imyownyear/Z-Butt/community_tools/4 Sprue Stem Cavity Reservoir Part/IMG_20200822_174101 - deagcaps.jpg

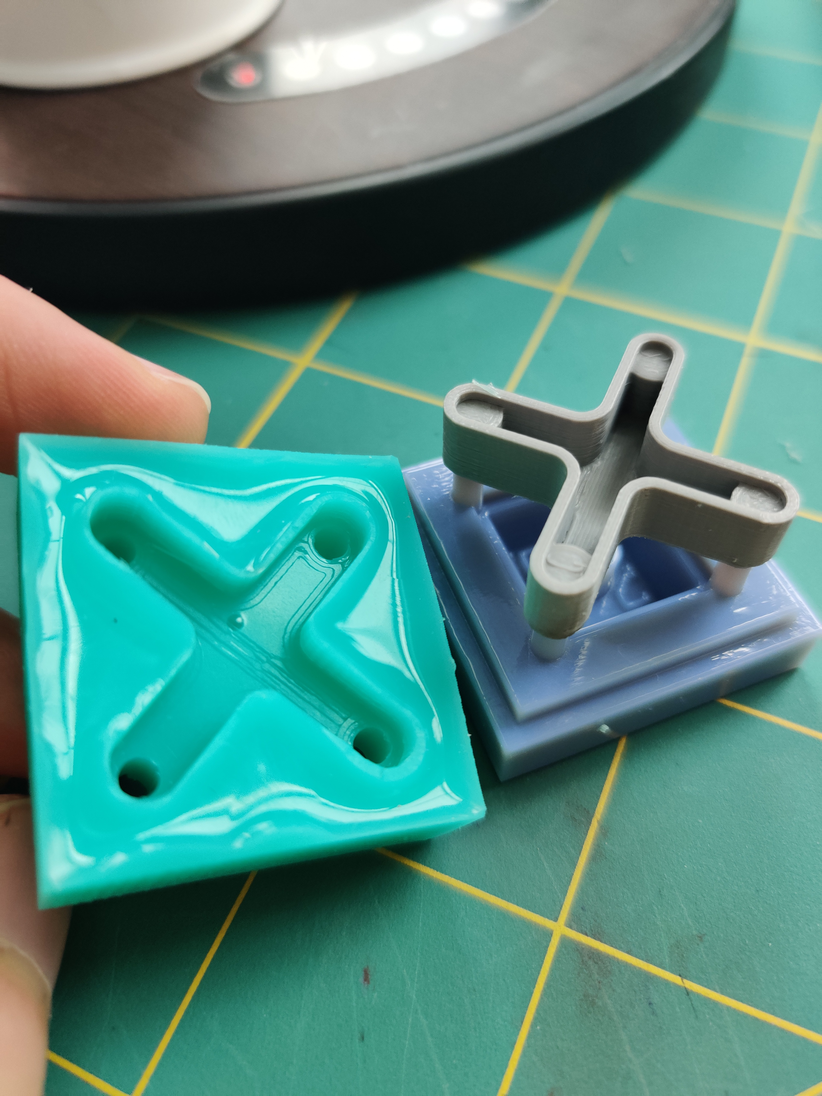
community_tools/4 Sprue Stem Cavity Reservoir Part/IMG_20200822_174101 - deagcaps.jpg
