imyownyear/Z-Butt/community_tools/6.25 Clone extender kit/20200730_202353 - Robert Maynard.jpg

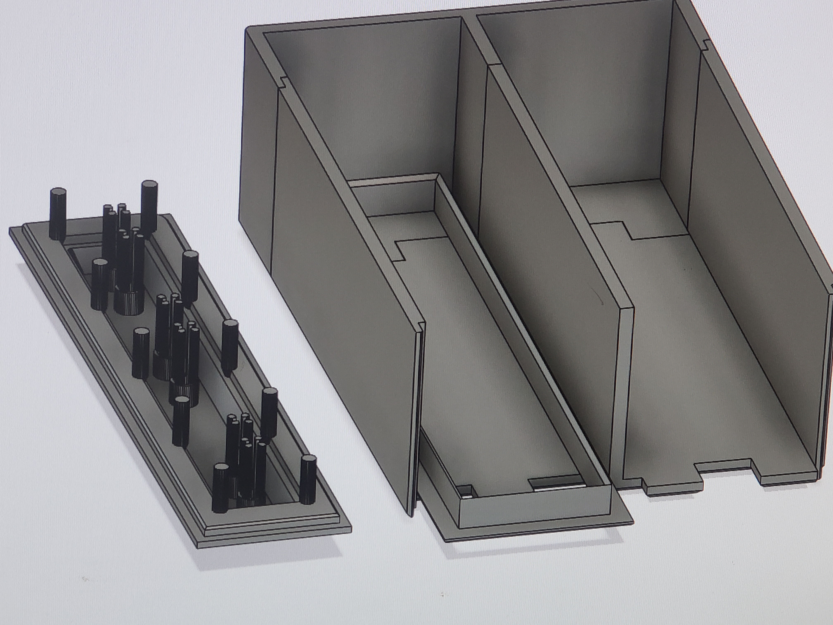
community_tools/6.25 Clone extender kit/20200730_202353 - Robert Maynard.jpg
