imyownyear/Z-Butt/MX/10-00u/ZButt-MasterBase-10u.stl

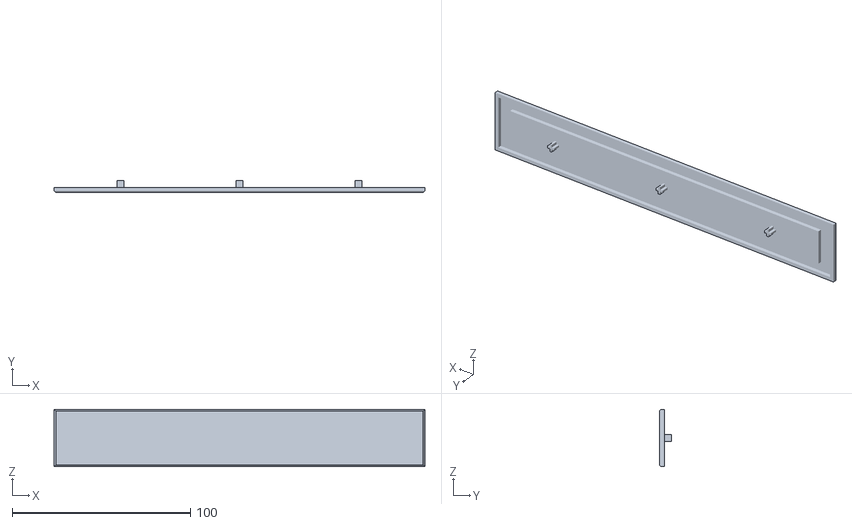
[picture p25: CAD file, 2021-09-04]
MX/10-00u/ZButt-MasterBase-10u.stl
208.0 x 7.00 x 32.0
