imyownyear/Z-Butt/MX/2-00u/V2/Reservoir.stl

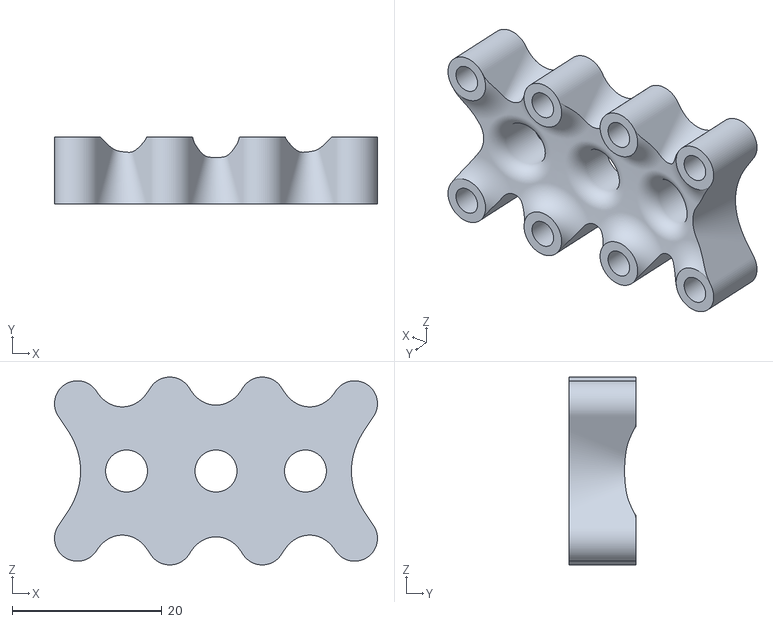
[picture p26: CAD file, 2023-01-14]
MX/2-00u/V2/Reservoir.stl
43.1 x 9.00 x 25.1
