imyownyear/Z-Butt/MX/2-25u/V2/Reservoir.stl

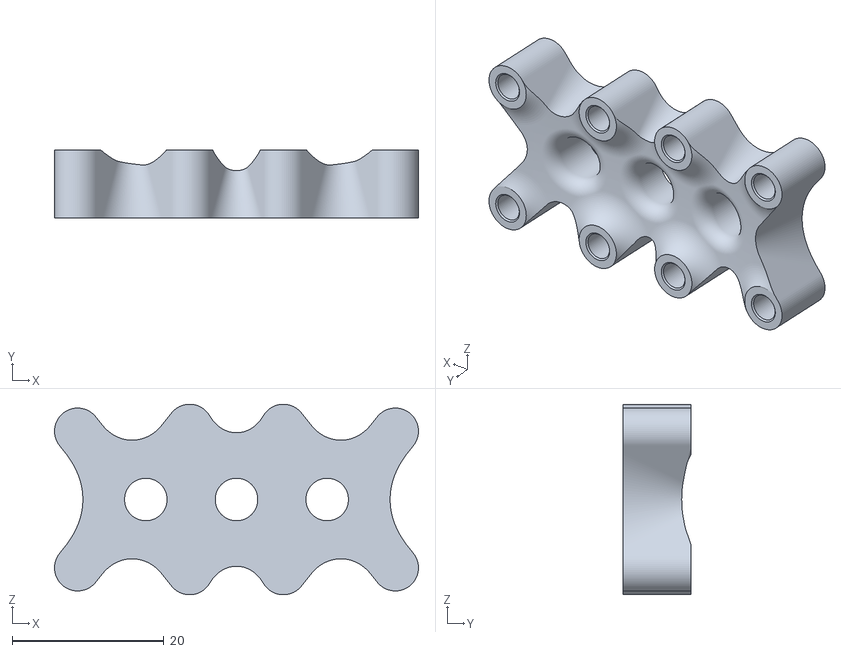
[picture p27: CAD file, 2023-01-14]
MX/2-25u/V2/Reservoir.stl
48.0 x 9.00 x 25.1
