imyownyear/Z-Butt/MX/2-50u/ZButt_2-5U_StemCavity.stl

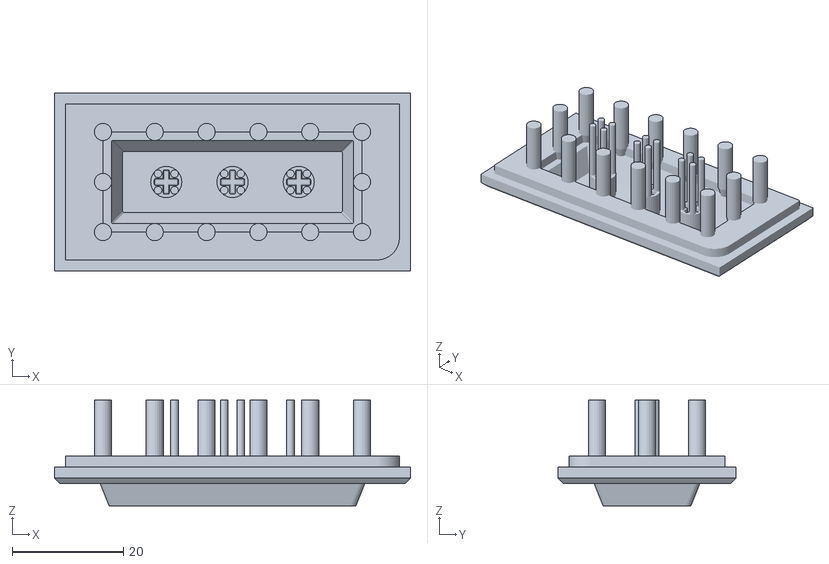
[picture p28: CAD file, 2019-06-22]
MX/2-50u/ZButt_2-5U_StemCavity.stl
64.0 x 32.0 x 19.0
