imyownyear/Z-Butt/MX/2-75u/V2/MasterBase.stl

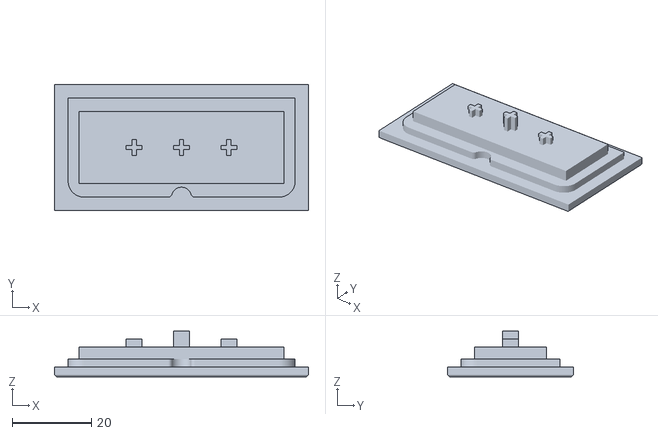
[picture p29: CAD file, 2023-01-14]
MX/2-75u/V2/MasterBase.stl
64.0 x 31.8 x 11.5
