imyownyear/Z-Butt/MX/3-00u/ZButt_3U_MasterBase.stl

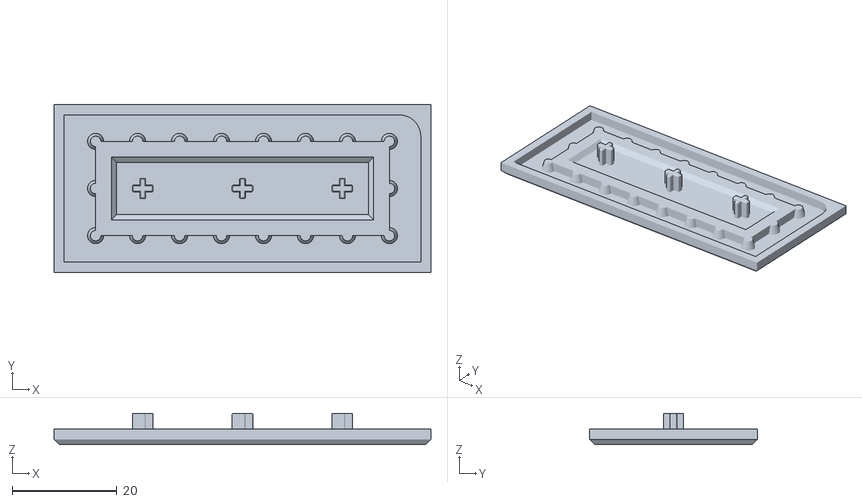
[picture p30: CAD file, 2019-06-22]
MX/3-00u/ZButt_3U_MasterBase.stl
72.0 x 32.0 x 6.00
