imyownyear/Z-Butt/MX/4-00u/ZButt_4U_StemCavity.stl

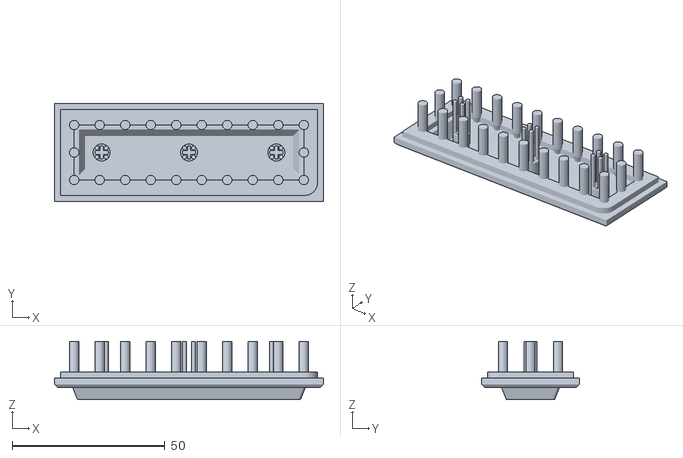
[picture p31: CAD file, 2019-06-22]
MX/4-00u/ZButt_4U_StemCavity.stl
88.0 x 32.0 x 19.0
