imyownyear/Z-Butt/MX/6-00u/ZButt_6U_StemCavity.stl

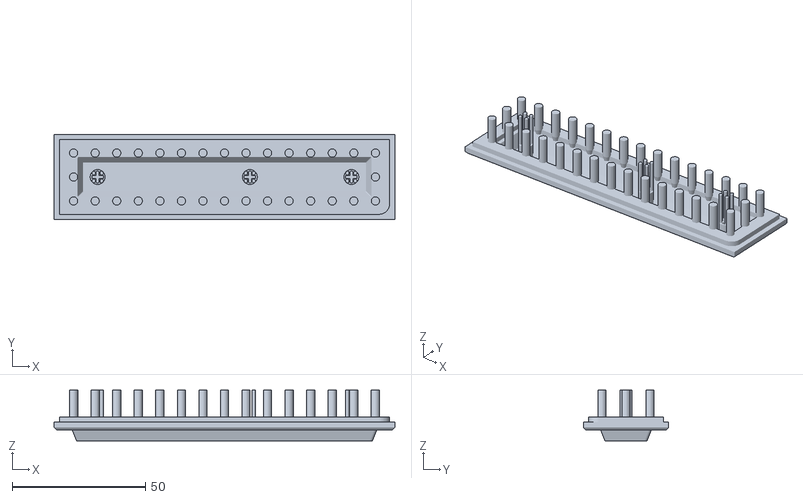
[picture p32: CAD file, 2019-06-22]
MX/6-00u/ZButt_6U_StemCavity.stl
128.0 x 32.0 x 19.0
