imyownyear/Z-Butt/MX/6-25u/V2/StemCavity.stl

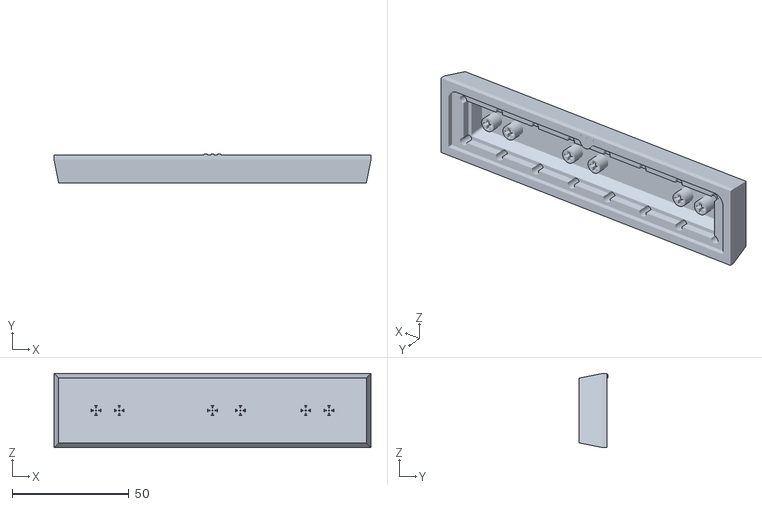
[picture p33: CAD file, 2023-01-14]
MX/6-25u/V2/StemCavity.stl
136.0 x 12.3 x 31.8
