imyownyear/Z-Butt/MX/7-00u/ZButt_7U_MasterBase.stl

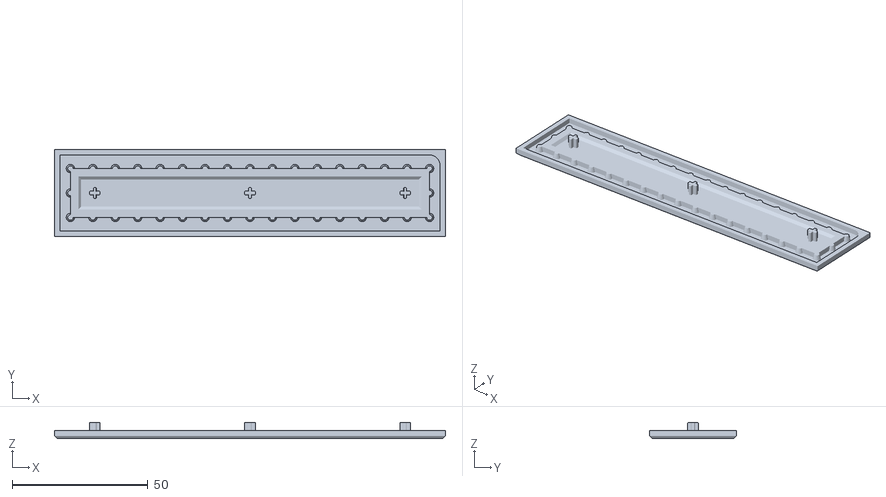
[picture p35: CAD file, 2019-06-22]
MX/7-00u/ZButt_7U_MasterBase.stl
144.0 x 32.0 x 6.00
