imyownyear/Z-Butt/MX/iso-enter/ZButt_ISO-ENTER_MasterBase-.stl

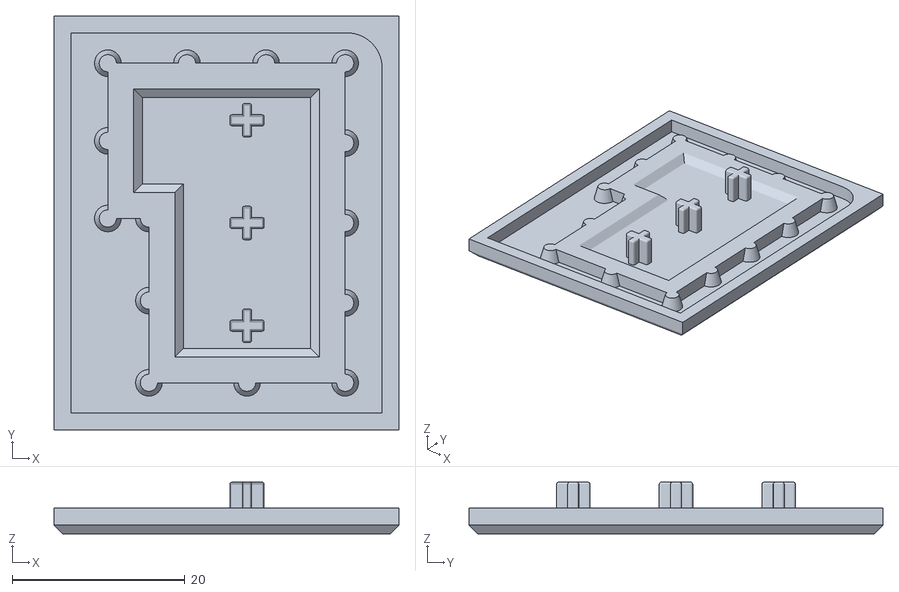
[picture p36: CAD file, 2019-07-23]
MX/iso-enter/ZButt_ISO-ENTER_MasterBase-.stl
40.0 x 48.0 x 6.00
