imyownyear/Z-Butt/NoHassleContainer/ISO-Enter-No-Hassle.stl

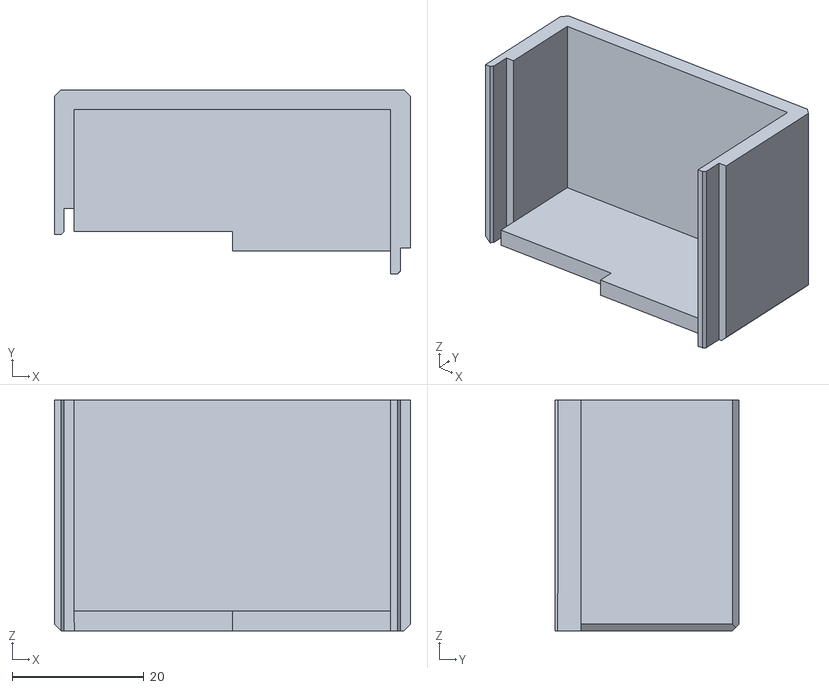
[picture p37: CAD file, 2020-08-27]
NoHassleContainer/ISO-Enter-No-Hassle.stl
54.0 x 28.0 x 35.0
