imyownyear/Z-Butt/TMX/ZButt-StemCavity.stl

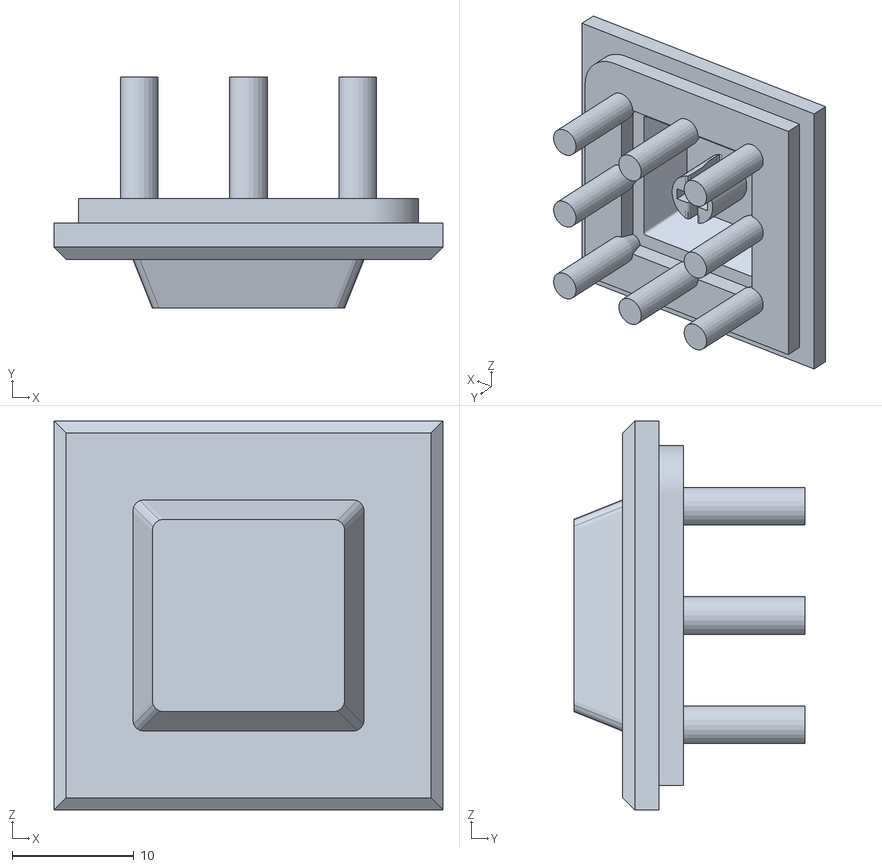
[picture p38: CAD file, 2019-08-04]
TMX/ZButt-StemCavity.stl
32.0 x 19.0 x 32.0
