imyownyear/Z-Butt/Topre/1u/v2/StemCavity.stl

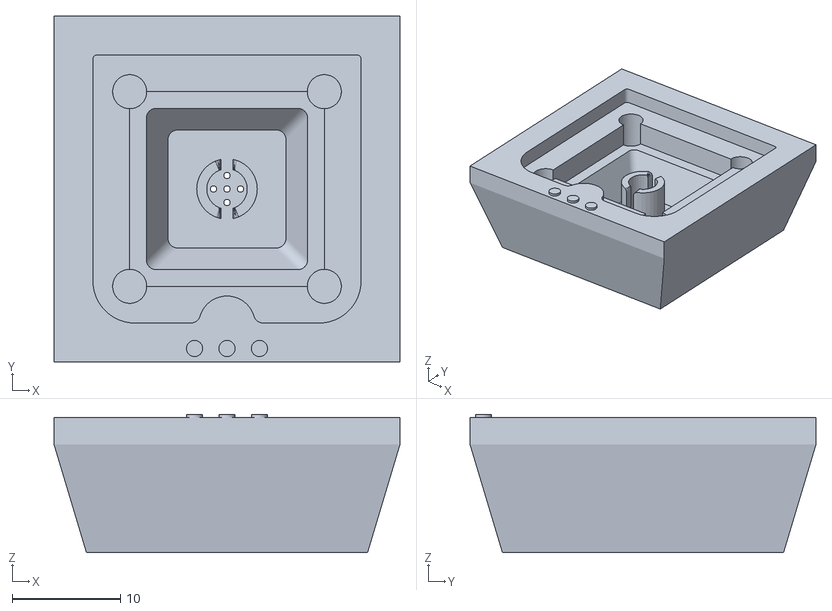
[picture p39: CAD file, 2023-01-14]
Topre/1u/v2/StemCavity.stl
32.0 x 32.0 x 12.8
