imyownyear/Z-Butt/AngleHolder/AngleHolder_4x4_A.stl

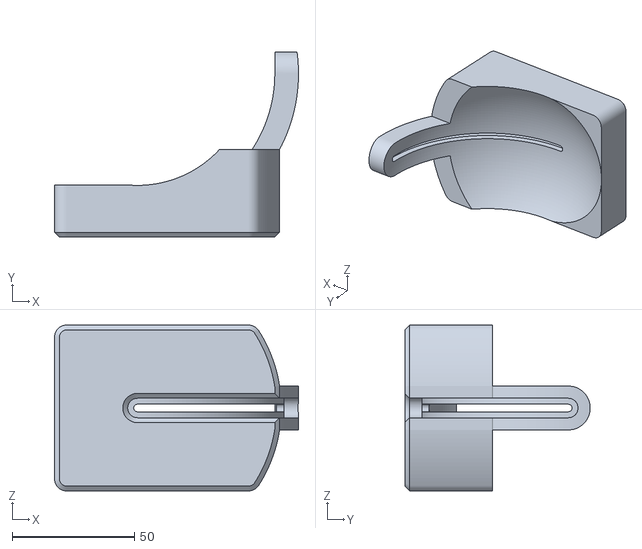
[picture p40: CAD file, 2020-08-14]
AngleHolder/AngleHolder_4x4_A.stl
100.0 x 76.0 x 68.0
