imyownyear/Z-Butt/Choc/1.5U/Choc_1.5U_SculptingBase.stl

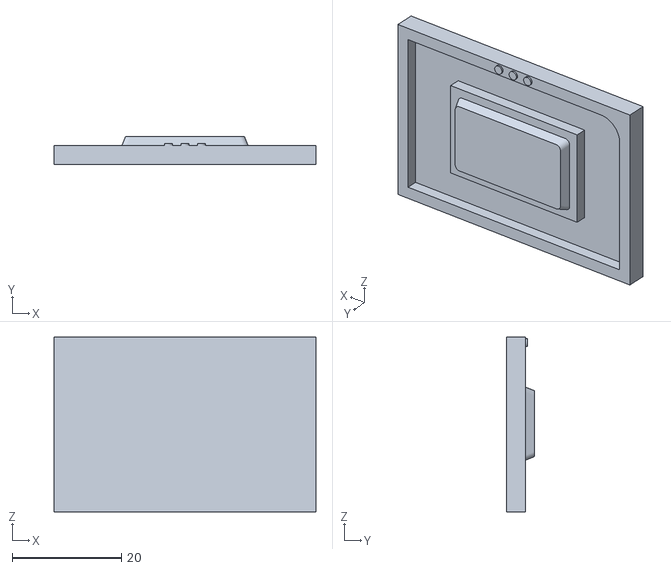
[picture p41: CAD file, 2021-09-04]
Choc/1.5U/Choc_1.5U_SculptingBase.stl
48.0 x 5.10 x 32.0
