imyownyear/Z-Butt/Choc/1U/Choc_1U_SculptingBase.stl

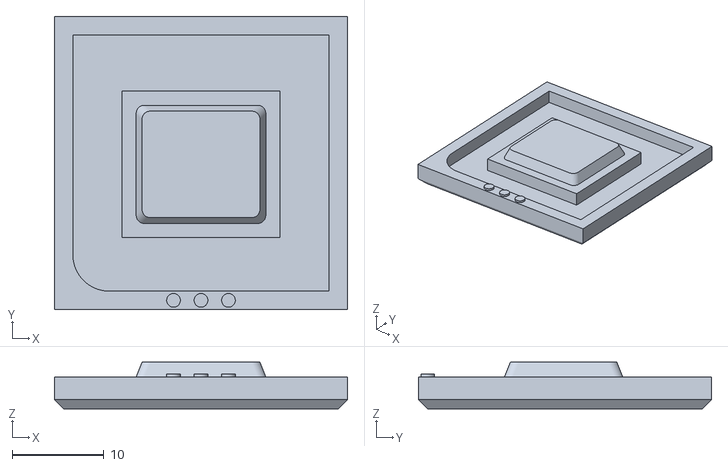
[picture p42: CAD file, 2021-09-04]
Choc/1U/Choc_1U_SculptingBase.stl
32.0 x 32.0 x 5.10
