imyownyear/Z-Butt/CloneRiser/1U/ZButt_2x2_CloneRiser_Cavity.stl

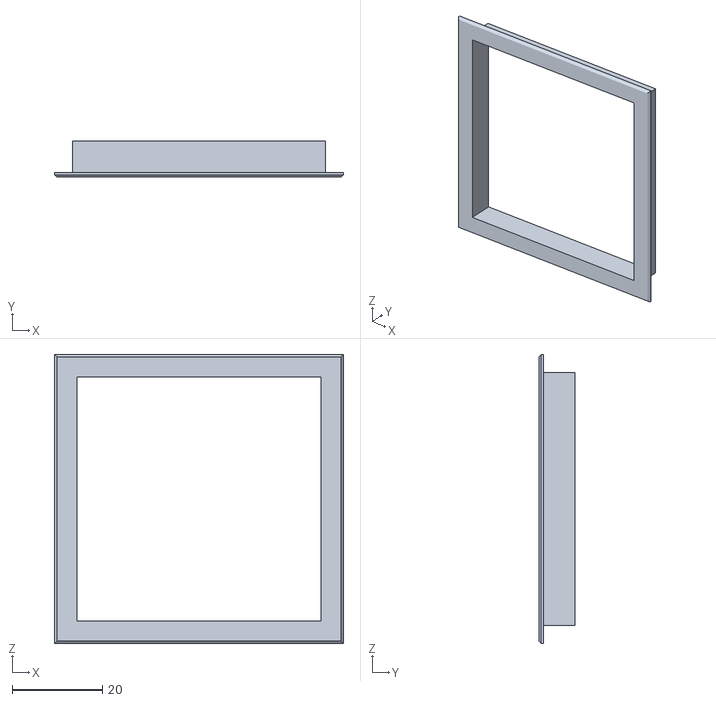
[picture p43: CAD file, 2023-01-14]
CloneRiser/1U/ZButt_2x2_CloneRiser_Cavity.stl
64.0 x 8.00 x 64.0
