imyownyear/Z-Butt/community_tools/2.75 stepped cap butt cavity and master base/Stepped Caps Stem Cavity - Robert Maynard.stl

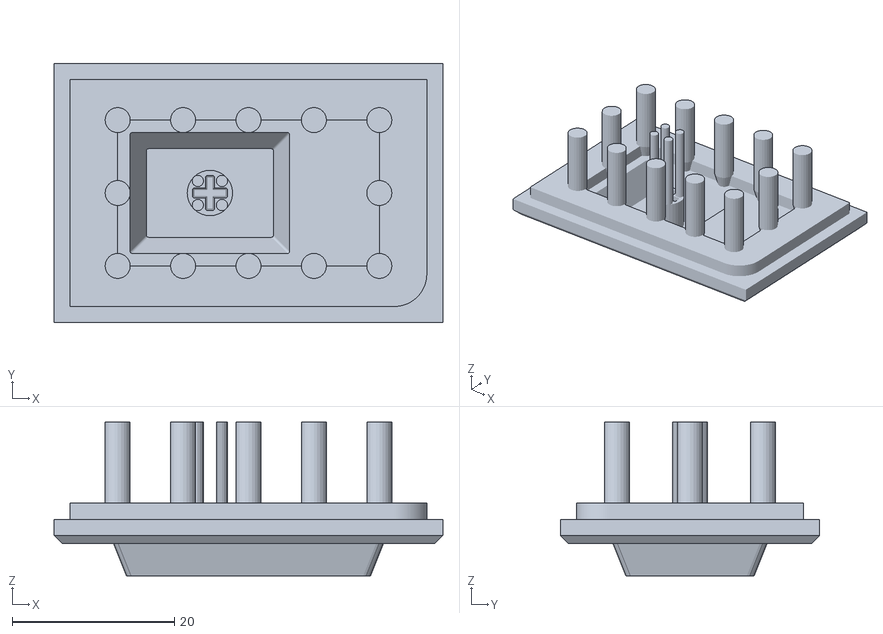
[picture p44: CAD file, 2020-09-03]
community_tools/2.75 stepped cap butt cavity and master base/Stepped Caps Stem Cavity - Robert Maynard.stl
48.0 x 32.0 x 19.0
