imyownyear/Z-Butt/community_tools/4 Sprue Stem Cavity Reservoir Part/Stem Reservoir 4 Sprue - deagcaps.STL

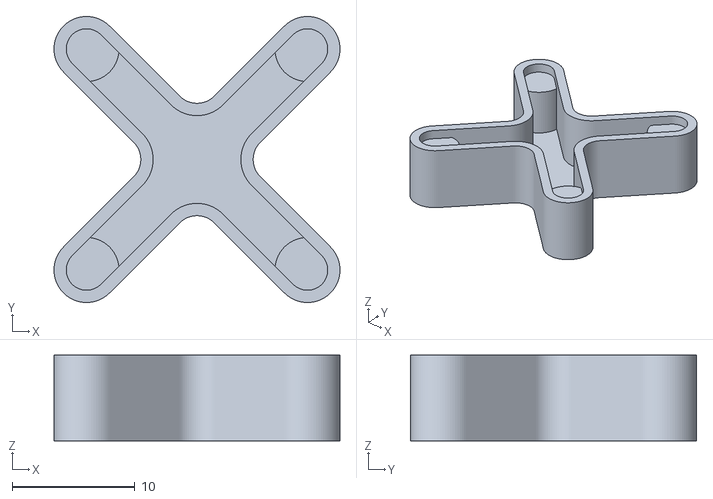
[picture p45: CAD file, 2020-09-03]
community_tools/4 Sprue Stem Cavity Reservoir Part/Stem Reservoir 4 Sprue - deagcaps.STL
23.3 x 23.3 x 7.00
