imyownyear/Z-Butt/community_tools/6.25 Clone extender kit/ZButt_6-25U_Clone_NoHassle_Extender - Robert Maynard.stl

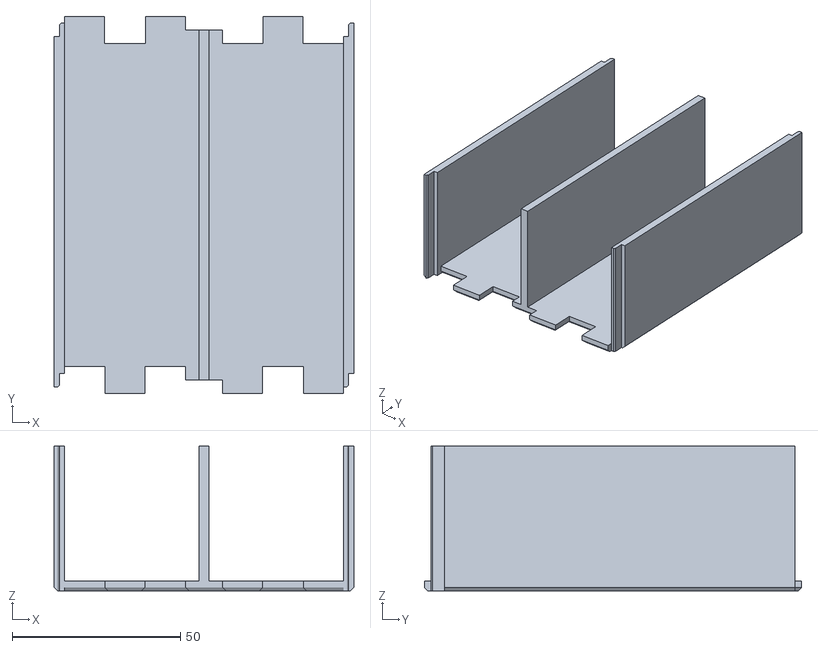
[picture p46: CAD file, 2020-09-03]
community_tools/6.25 Clone extender kit/ZButt_6-25U_Clone_NoHassle_Extender - Robert Maynard.stl
89.0 x 112.0 x 43.0
