imyownyear/Z-Butt/community_tools/Gooseneck syringe tip handle/gooseneck handle.STL

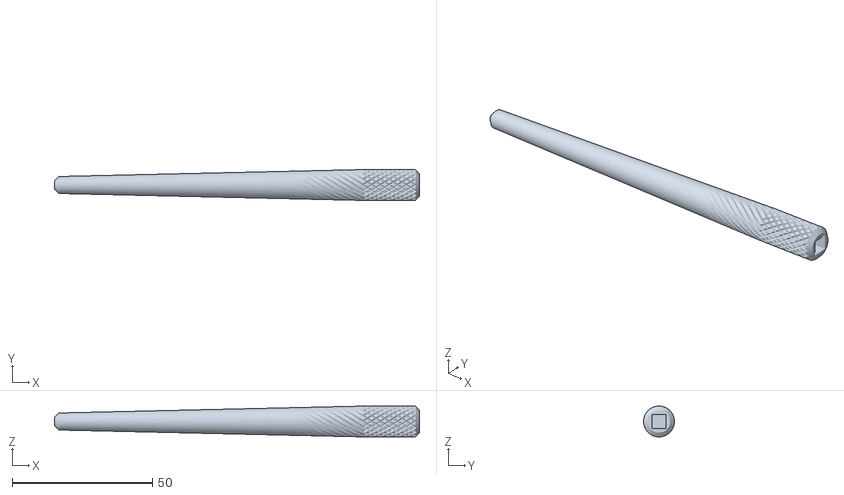
[picture p47: CAD file, 2020-09-03]
community_tools/Gooseneck syringe tip handle/gooseneck handle.STL
130.0 x 11.0 x 11.0
