imyownyear/Z-Butt/MX/1-00u/1u - Production/NoHassle2x3Extend.stl

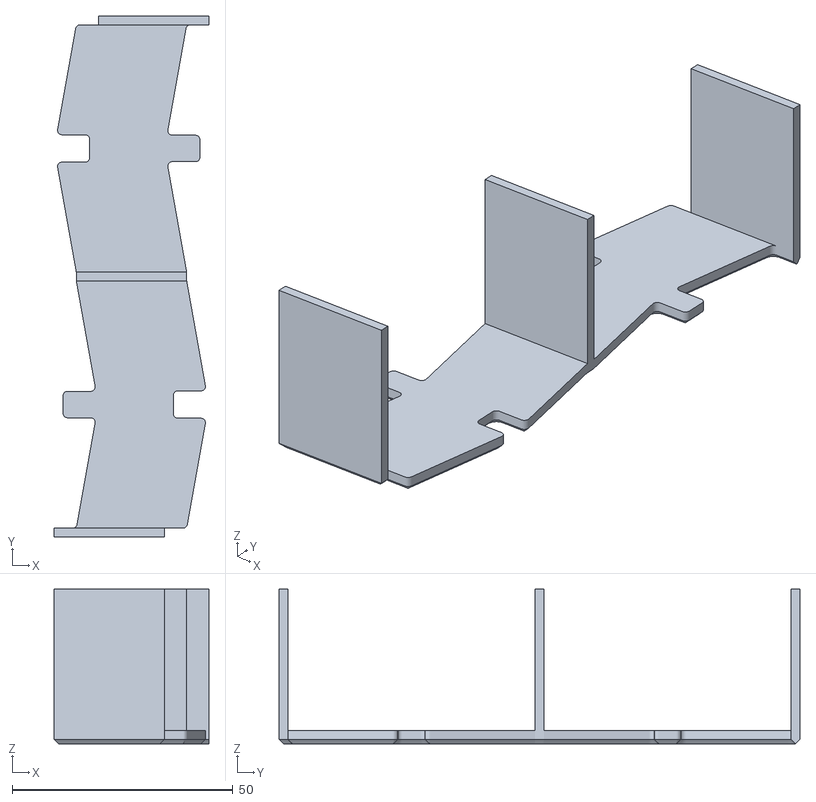
[picture p48: CAD file, 2021-12-05]
MX/1-00u/1u - Production/NoHassle2x3Extend.stl
35.0 x 118.0 x 35.0
