imyownyear/Z-Butt/MX/1-25u/V2/MasterBase.stl

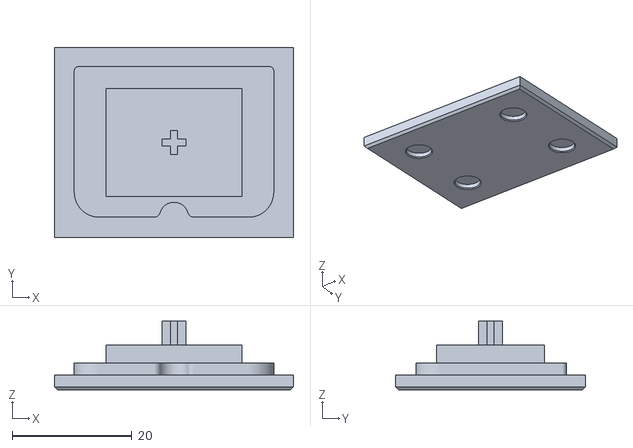
[picture p49: CAD file, 2023-01-14]
MX/1-25u/V2/MasterBase.stl
40.0 x 31.8 x 11.5
