imyownyear/Z-Butt/MX/1-50u/V2/StemCavity-Recessed.stl

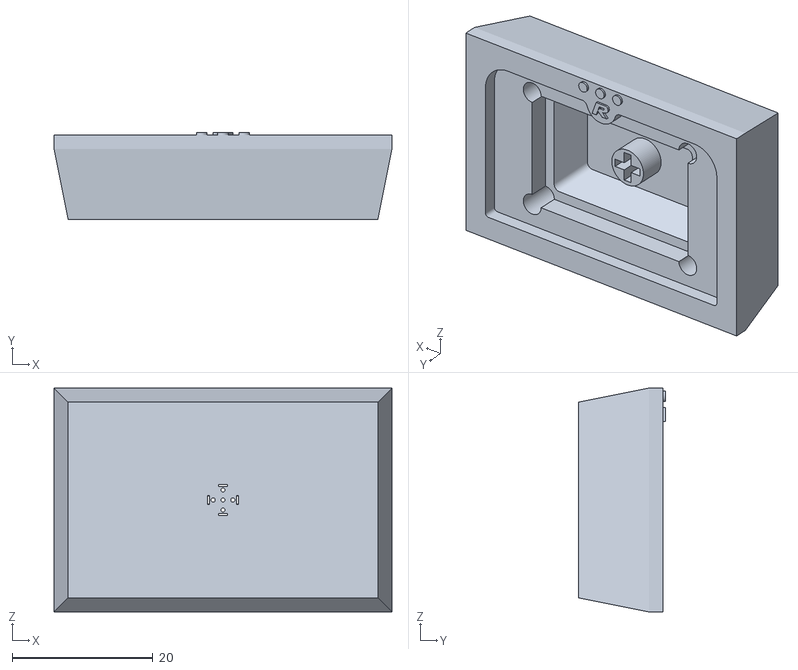
[picture p50: CAD file, 2023-01-14]
MX/1-50u/V2/StemCavity-Recessed.stl
48.0 x 12.3 x 31.8
