imyownyear/Z-Butt/MX/10-00u/ZButt-StemCavity-10u-Sprue.stl

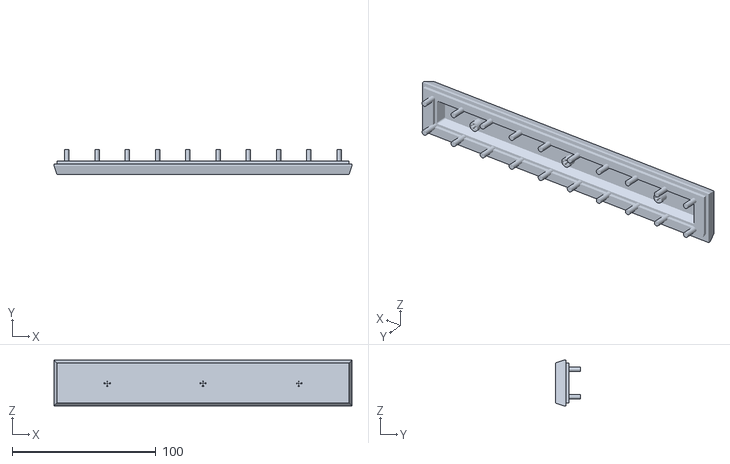
[picture p52: CAD file, 2021-09-04]
MX/10-00u/ZButt-StemCavity-10u-Sprue.stl
207.4 x 17.5 x 32.0
