imyownyear/Z-Butt/MX/2-25u/V2/StemCavity.stl

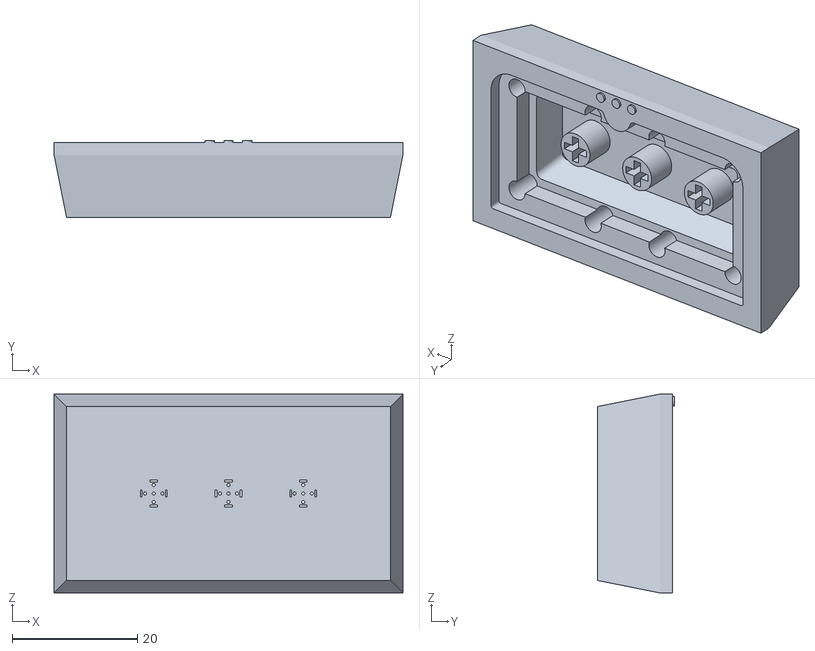
[picture p54: CAD file, 2023-01-14]
MX/2-25u/V2/StemCavity.stl
55.8 x 12.3 x 31.8
