imyownyear/Z-Butt/MX/2-75u/V2/StemCavity-Recessed.stl

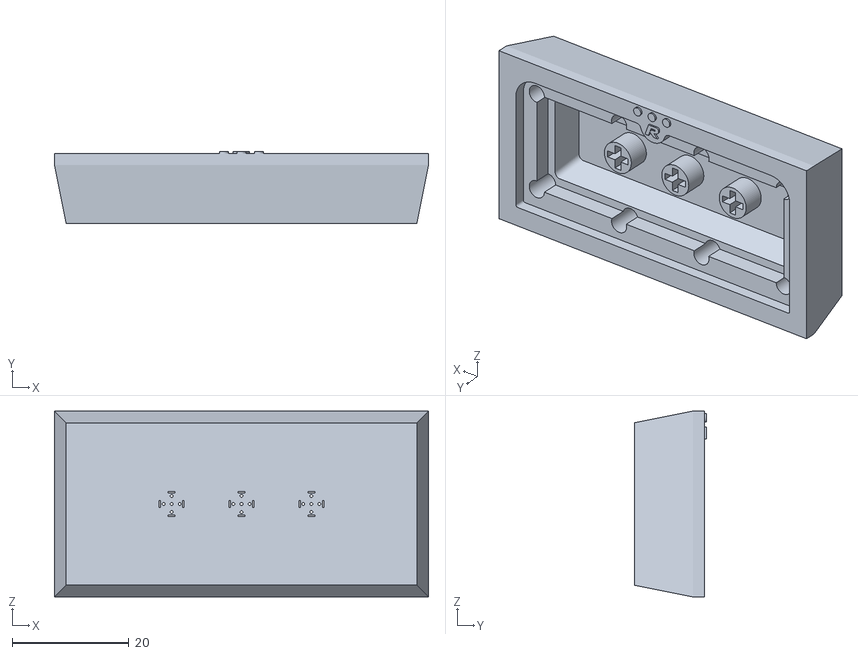
[picture p56: CAD file, 2023-01-14]
MX/2-75u/V2/StemCavity-Recessed.stl
64.0 x 12.3 x 31.8
