imyownyear/Z-Butt/MX/3-00u/ZButt_3U_StemCavity.stl

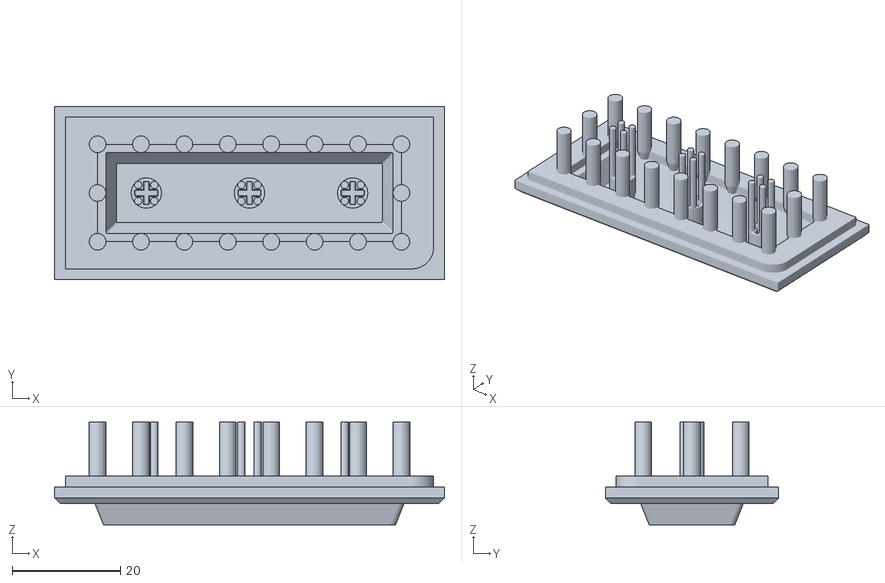
[picture p57: CAD file, 2019-06-22]
MX/3-00u/ZButt_3U_StemCavity.stl
72.0 x 32.0 x 19.0
