imyownyear/Z-Butt/MX/4-00u/ZButt_4U_SculptingBase.stl

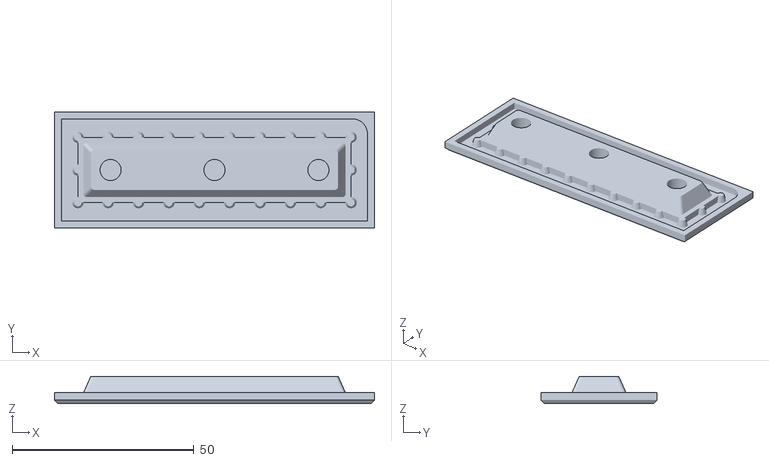
[picture p58: CAD file, 2019-06-22]
MX/4-00u/ZButt_4U_SculptingBase.stl
88.0 x 32.0 x 7.50
