imyownyear/Z-Butt/MX/6-00u/ZButt_6U_SculptingBase.stl

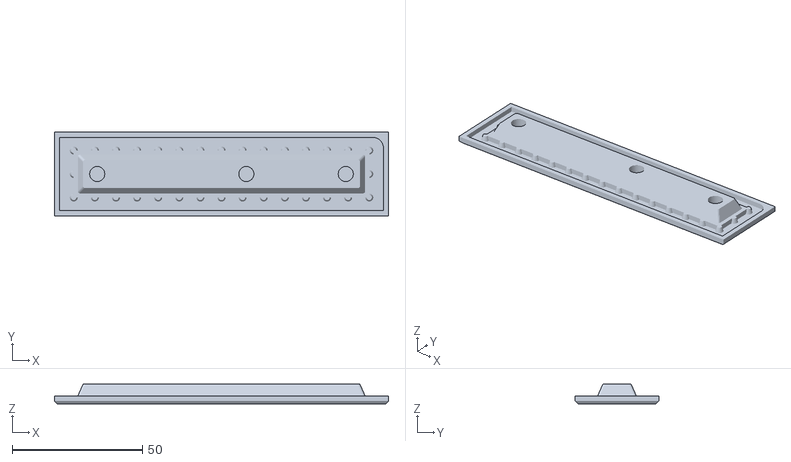
[picture p59: CAD file, 2019-06-22]
MX/6-00u/ZButt_6U_SculptingBase.stl
128.0 x 32.0 x 7.50
