imyownyear/Z-Butt/MX/6-25u/V2/MasterBase.stl

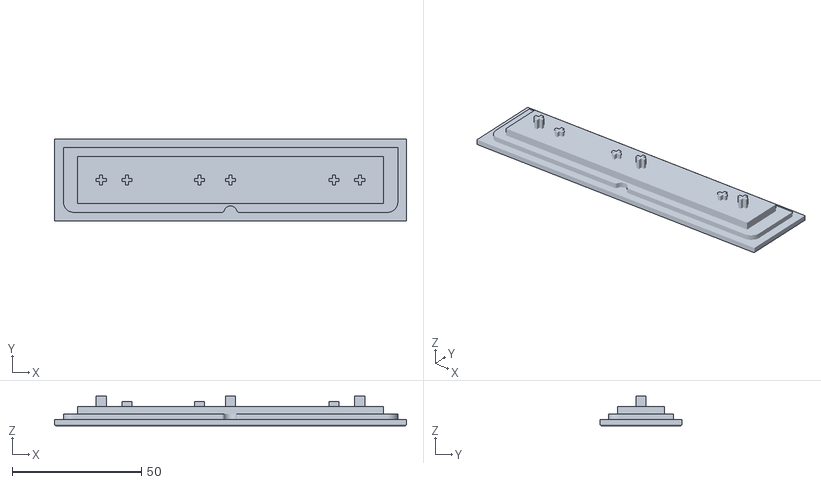
[picture p60: CAD file, 2023-01-14]
MX/6-25u/V2/MasterBase.stl
136.0 x 31.8 x 11.5
