imyownyear/Z-Butt/MX/7-00u/ZButt_7U_SculptingBase.stl

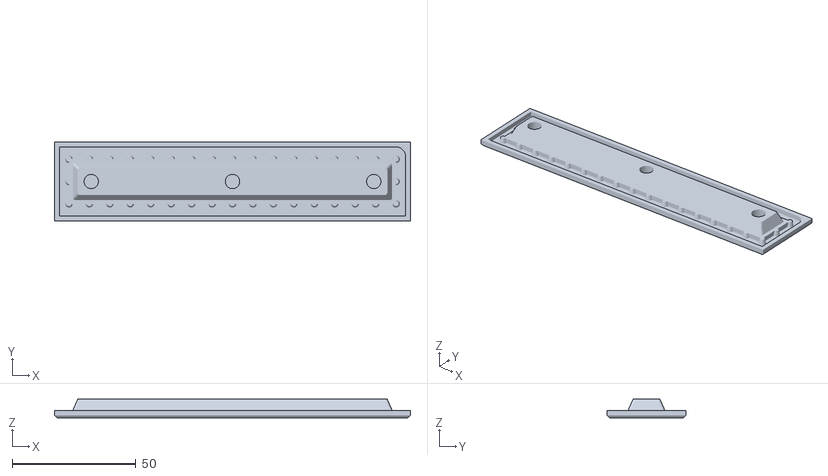
[picture p62: CAD file, 2019-06-22]
MX/7-00u/ZButt_7U_SculptingBase.stl
144.0 x 32.0 x 7.50
