imyownyear/Z-Butt/MX/iso-enter/ZButt_ISO-ENTER_SculptingBase-.stl

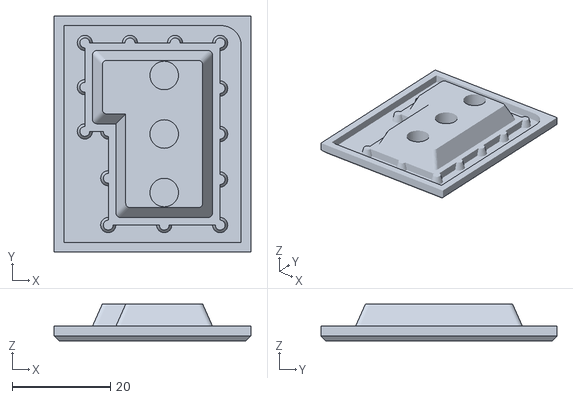
[picture p63: CAD file, 2019-07-23]
MX/iso-enter/ZButt_ISO-ENTER_SculptingBase-.stl
40.0 x 48.0 x 7.50
