imyownyear/Z-Butt/NoHassleContainer/1.25U-1.5U-No-Hassle.STL

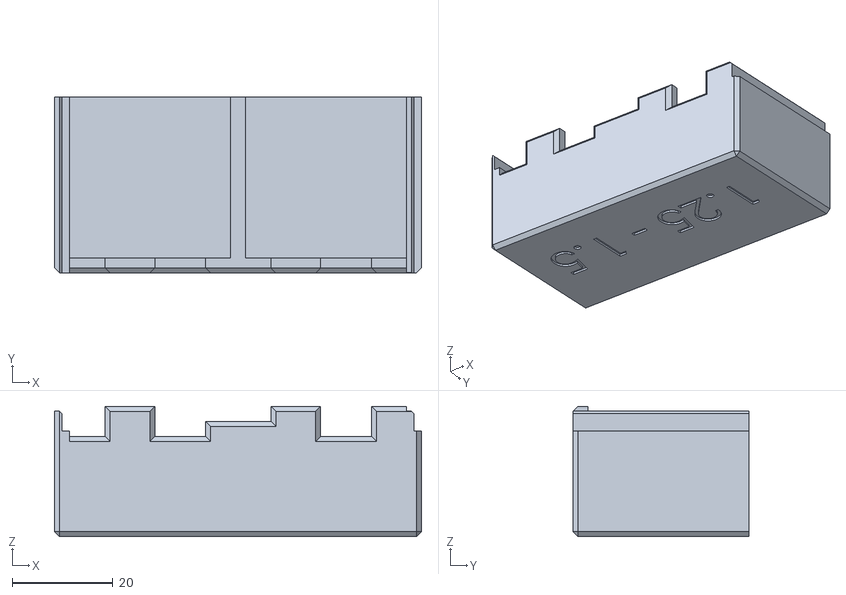
[picture p64: CAD file, 2020-07-30]
NoHassleContainer/1.25U-1.5U-No-Hassle.STL
73.0 x 35.0 x 26.0
