imyownyear/Z-Butt/AngleHolder/AngleHolder_1x1U.stl

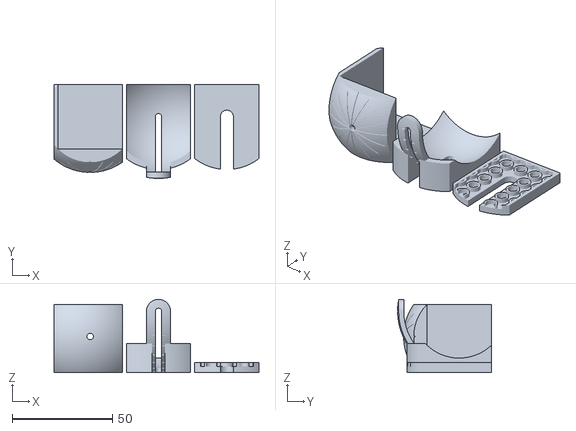
[picture p65: CAD file, 2020-08-12]
AngleHolder/AngleHolder_1x1U.stl
102.0 x 46.7 x 36.5
