imyownyear/Z-Butt/Choc/1U/Choc_1U_MasterBase.stl

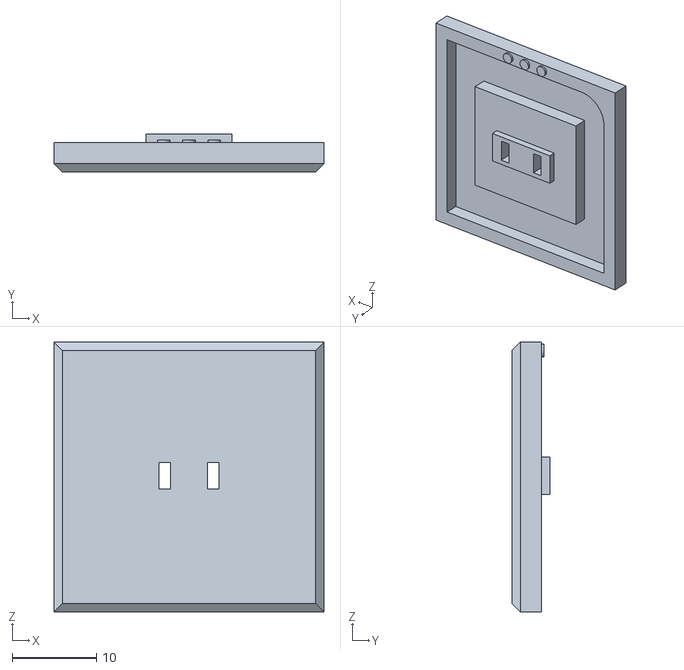
[picture p66: CAD file, 2021-09-04]
Choc/1U/Choc_1U_MasterBase.stl
32.0 x 4.50 x 32.0
