imyownyear/Z-Butt/Choc/2U/Choc_2U_StemCavity.stl

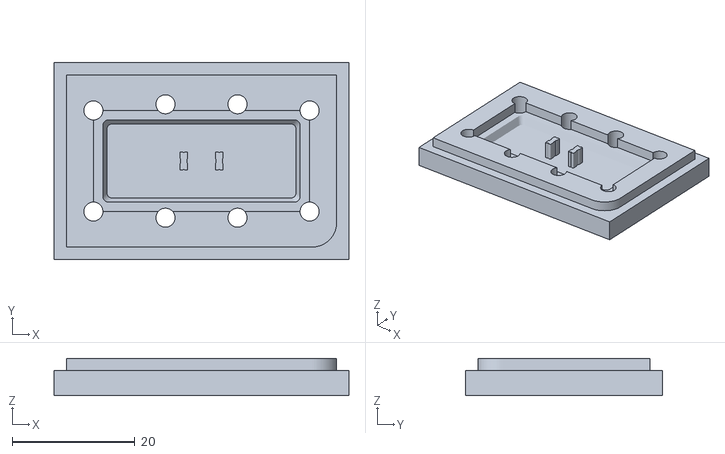
[picture p67: CAD file, 2021-09-04]
Choc/2U/Choc_2U_StemCavity.stl
48.0 x 32.0 x 6.10
