imyownyear/Z-Butt/CloneRiser/1U/ZButt_1U_Clone_NoHassle.STL

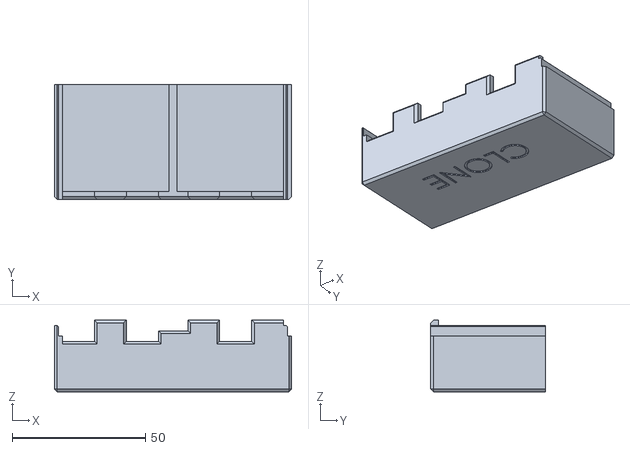
[picture p68: CAD file, 2020-02-06]
CloneRiser/1U/ZButt_1U_Clone_NoHassle.STL
89.0 x 43.0 x 27.0
