imyownyear/Z-Butt/community_tools/6.25 Clone extender kit/ZButt_6-25U_CloneRiser_Master - Robert Maynard.stl

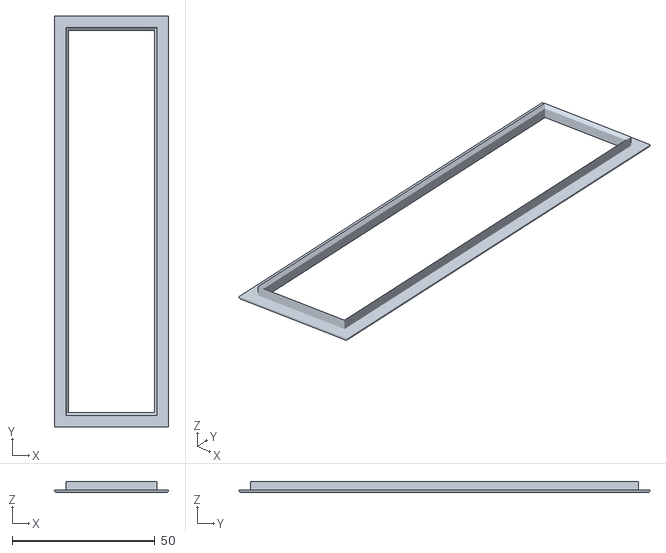
[picture p69: CAD file, 2020-09-03]
community_tools/6.25 Clone extender kit/ZButt_6-25U_CloneRiser_Master - Robert Maynard.stl
40.0 x 144.0 x 4.00
