imyownyear/Z-Butt/MX/1-00u/1u - Production/ZButt-StemCavity-2x3-Recessed.stl

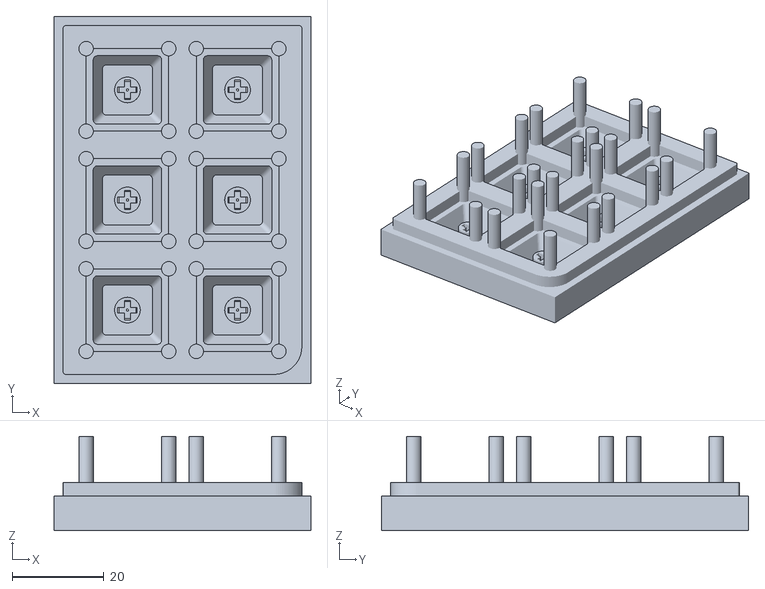
[picture p70: CAD file, 2021-11-26]
MX/1-00u/1u - Production/ZButt-StemCavity-2x3-Recessed.stl
56.0 x 80.0 x 20.5
