imyownyear/Z-Butt/MX/1-00u/1u-V2/1u-Resevoir-Topper-0.3.stl

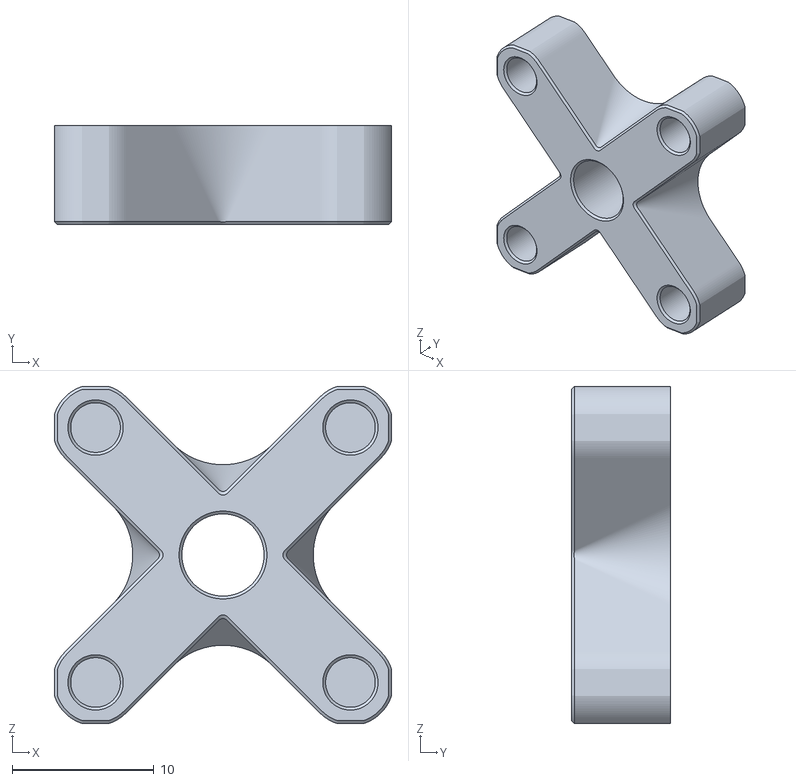
[picture p71: CAD file, 2021-03-12]
MX/1-00u/1u-V2/1u-Resevoir-Topper-0.3.stl
23.8 x 7.00 x 23.8
