imyownyear/Z-Butt/MX/1-25u/V2/Reservoir.stl

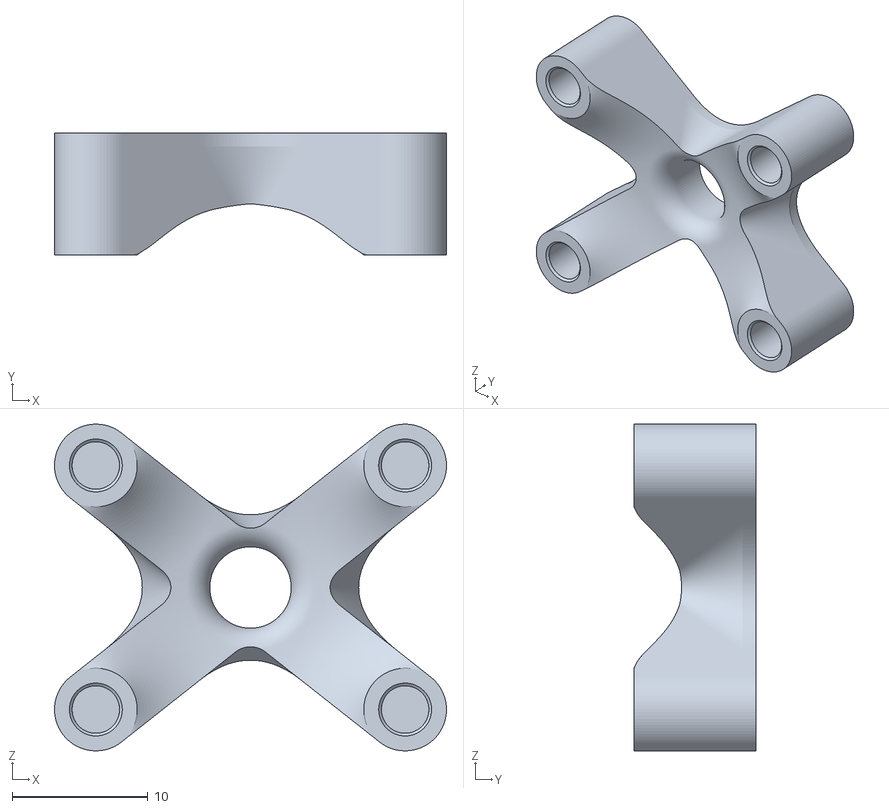
[picture p72: CAD file, 2023-01-14]
MX/1-25u/V2/Reservoir.stl
28.9 x 9.00 x 24.1
