imyownyear/Z-Butt/MX/1-50u/V2/MasterBase.stl

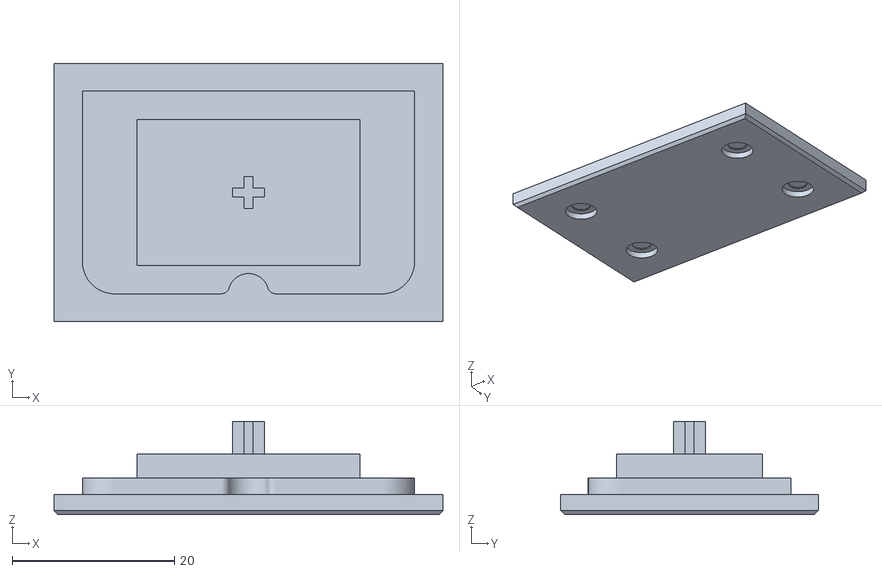
[picture p73: CAD file, 2023-01-14]
MX/1-50u/V2/MasterBase.stl
48.0 x 31.8 x 11.5
