imyownyear/Z-Butt/MX/1-75u/V2/StemCavity.stl

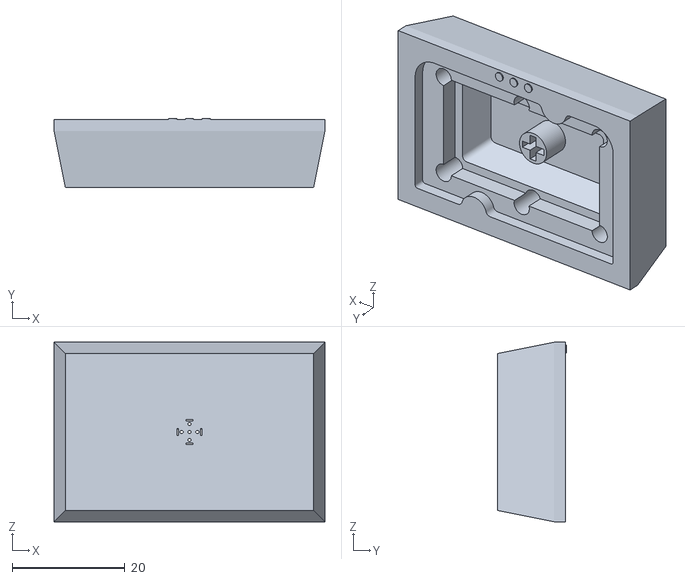
[picture p74: CAD file, 2023-01-14]
MX/1-75u/V2/StemCavity.stl
48.0 x 12.2 x 31.8
