imyownyear/Z-Butt/MX/10-00u/Zbutt-SculptingBase-10u.stl

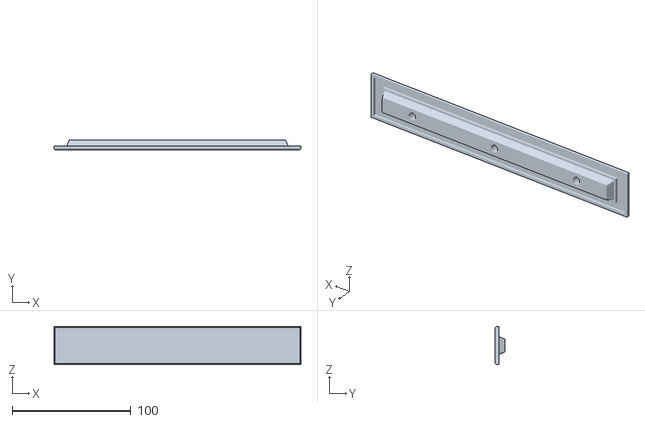
[picture p75: CAD file, 2021-09-04]
MX/10-00u/Zbutt-SculptingBase-10u.stl
208.0 x 8.00 x 32.0
