imyownyear/Z-Butt/MX/2-00u/V2/MasterBase.stl

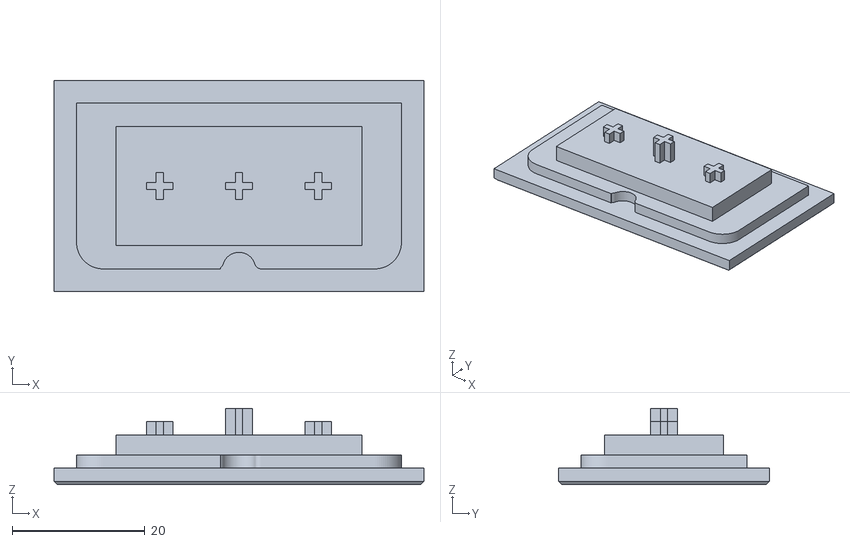
[picture p76: CAD file, 2023-01-14]
MX/2-00u/V2/MasterBase.stl
55.8 x 31.8 x 11.5
