imyownyear/Z-Butt/MX/2-50u/ZButt_2-5U_SculptingBase.stl

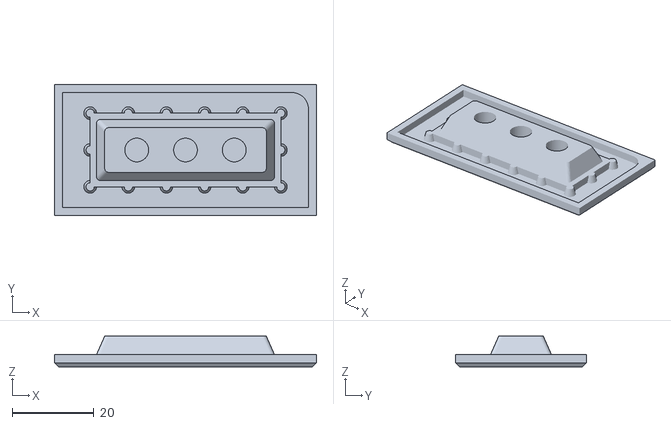
[picture p77: CAD file, 2019-06-22]
MX/2-50u/ZButt_2-5U_SculptingBase.stl
64.0 x 32.0 x 7.50
