imyownyear/Z-Butt/MX/2-75u/V2/Reservoir.stl

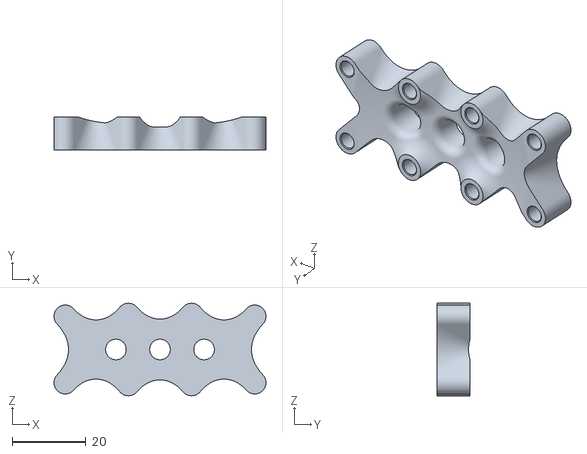
[picture p78: CAD file, 2023-01-14]
MX/2-75u/V2/Reservoir.stl
57.5 x 9.00 x 25.1
