imyownyear/Z-Butt/MX/3-00u/ZButt_3U_SculptingBase.stl

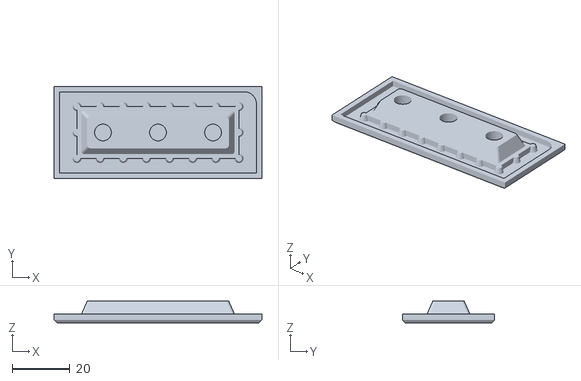
[picture p79: CAD file, 2019-06-22]
MX/3-00u/ZButt_3U_SculptingBase.stl
72.0 x 32.0 x 7.50
