imyownyear/Z-Butt/MX/4-00u/ZButt_4U_MasterBase.stl

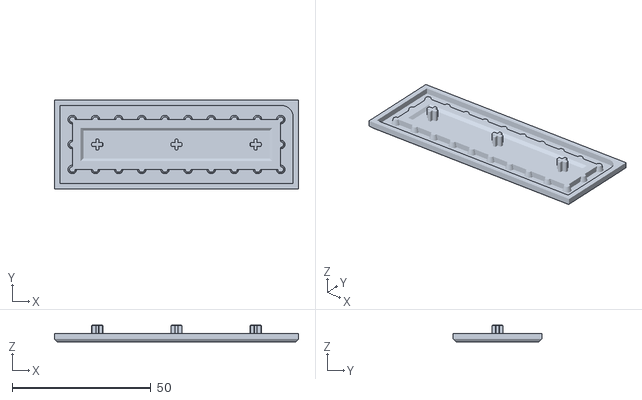
[picture p80: CAD file, 2019-06-22]
MX/4-00u/ZButt_4U_MasterBase.stl
88.0 x 32.0 x 6.00
