imyownyear/Z-Butt/MX/6-00u/ZButt_6U_MasterBase.stl

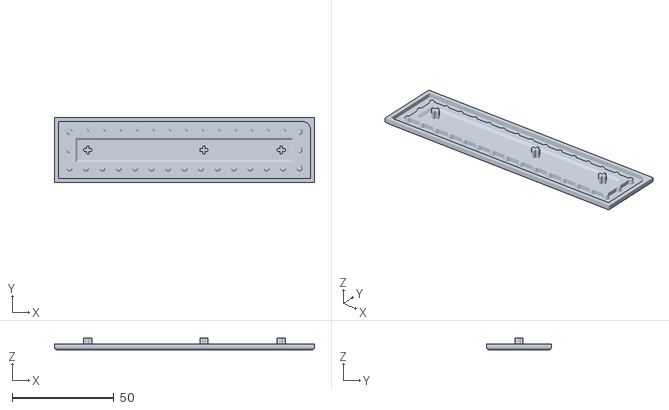
[picture p81: CAD file, 2019-06-22]
MX/6-00u/ZButt_6U_MasterBase.stl
128.0 x 32.0 x 6.00
