imyownyear/Z-Butt/MX/6-25u/V2/SculptingBase.stl

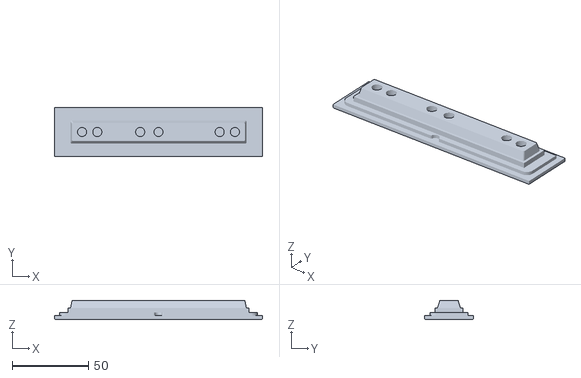
[picture p82: CAD file, 2023-01-14]
MX/6-25u/V2/SculptingBase.stl
136.0 x 31.8 x 12.5
