imyownyear/Z-Butt/MX/6-50u/SA-6.5u-OnMasterBase.stl

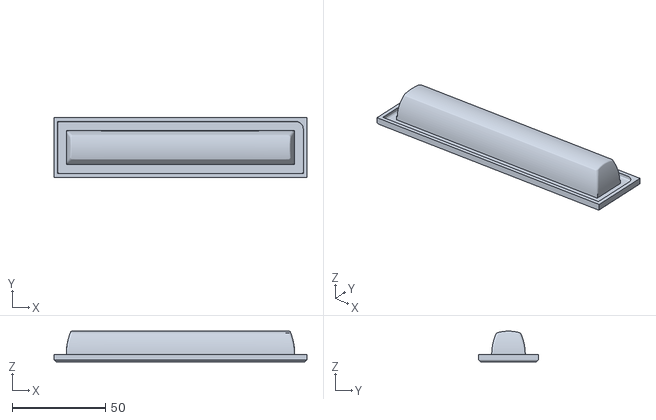
[picture p83: CAD file, 2021-09-03]
MX/6-50u/SA-6.5u-OnMasterBase.stl
136.0 x 32.0 x 16.5
