imyownyear/Z-Butt/MX/7-00u/ZButt_7U_StemCavity.stl

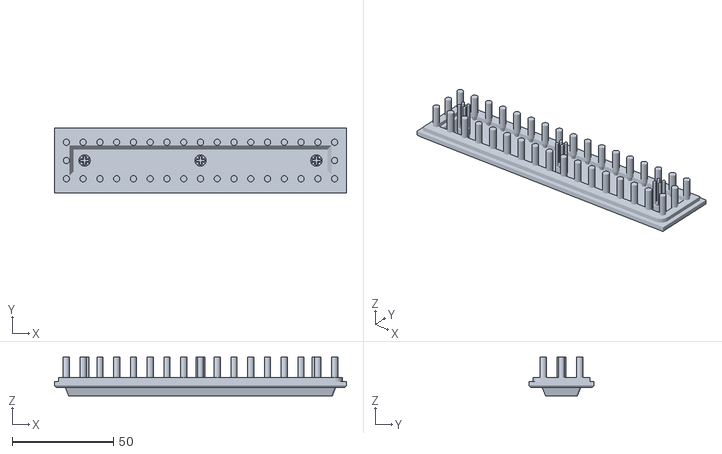
[picture p84: CAD file, 2019-06-22]
MX/7-00u/ZButt_7U_StemCavity.stl
144.0 x 32.0 x 19.0
