imyownyear/Z-Butt/MX/iso-enter/ZButt_ISO-ENTER_StemCavity-.stl

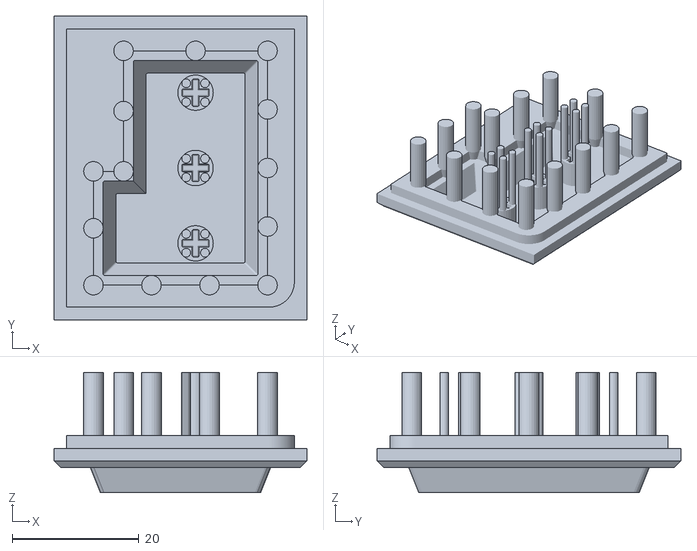
[picture p85: CAD file, 2019-07-23]
MX/iso-enter/ZButt_ISO-ENTER_StemCavity-.stl
40.0 x 48.0 x 19.0
