imyownyear/Z-Butt/NoHassleContainer/2.50U-2.75U-No-Hassle.STL

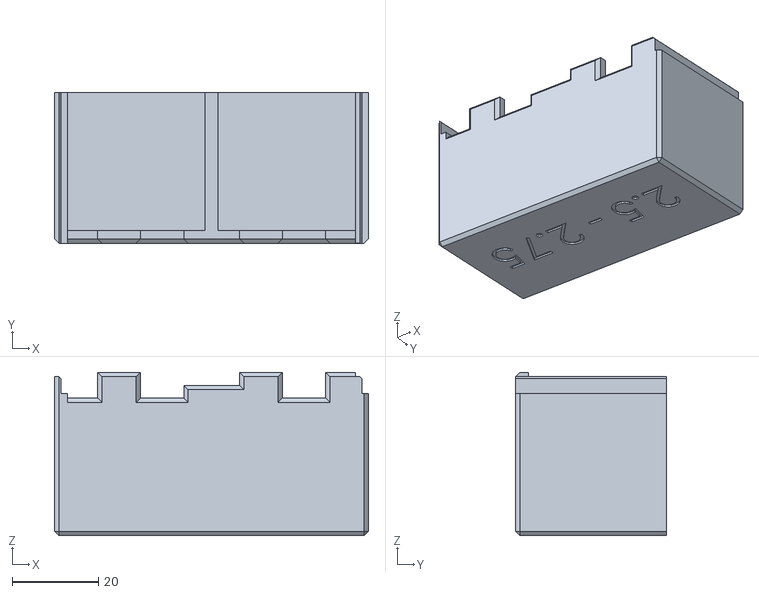
[picture p86: CAD file, 2020-07-30]
NoHassleContainer/2.50U-2.75U-No-Hassle.STL
73.0 x 35.0 x 38.0
