imyownyear/Z-Butt/CloneRiser/1U/ZButt_1U_CloneRiser_Master.stl

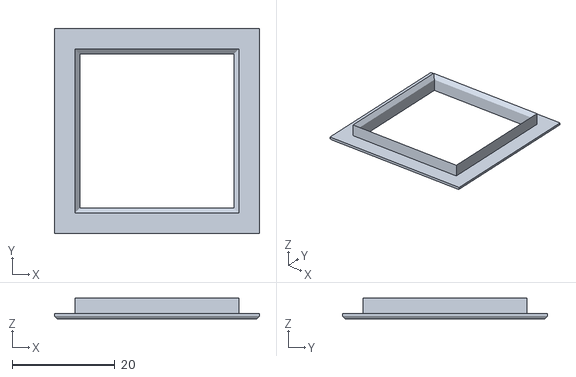
[picture p87: CAD file, 2019-08-20]
CloneRiser/1U/ZButt_1U_CloneRiser_Master.stl
40.0 x 40.0 x 4.00
