imyownyear/Z-Butt/MX/1-00u/1u - Production/ZButt-MasterBase-2x3 .stl

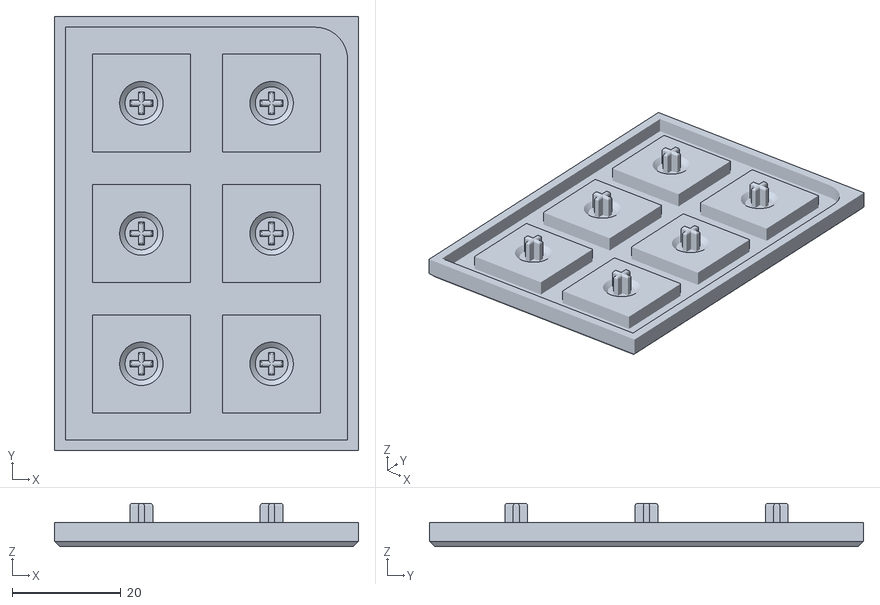
[picture p88: CAD file, 2021-11-26]
MX/1-00u/1u - Production/ZButt-MasterBase-2x3 .stl
56.0 x 80.0 x 8.00
