imyownyear/Z-Butt/MX/1-00u/1u-V2/MasterBase.stl

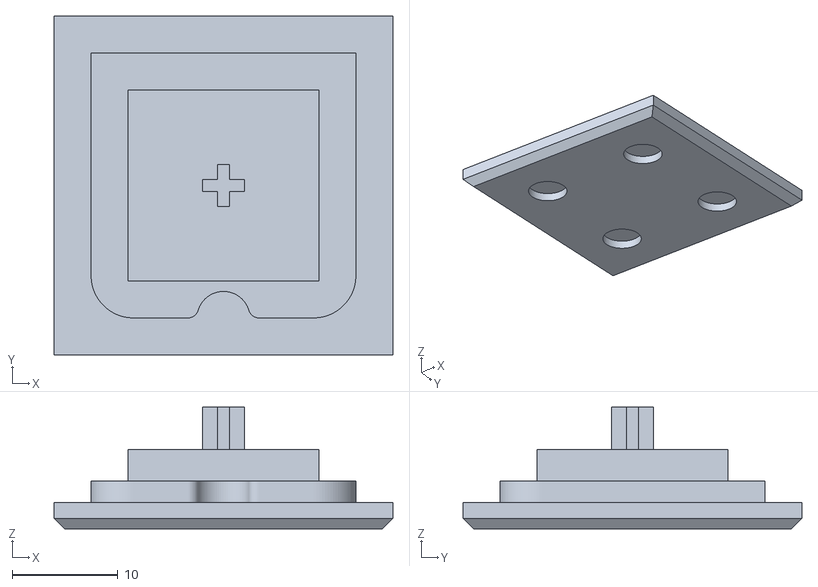
[picture p89: CAD file, 2021-03-12]
MX/1-00u/1u-V2/MasterBase.stl
32.0 x 32.0 x 11.5
