imyownyear/Z-Butt/MX/1-25u/V2/StemCavity.stl

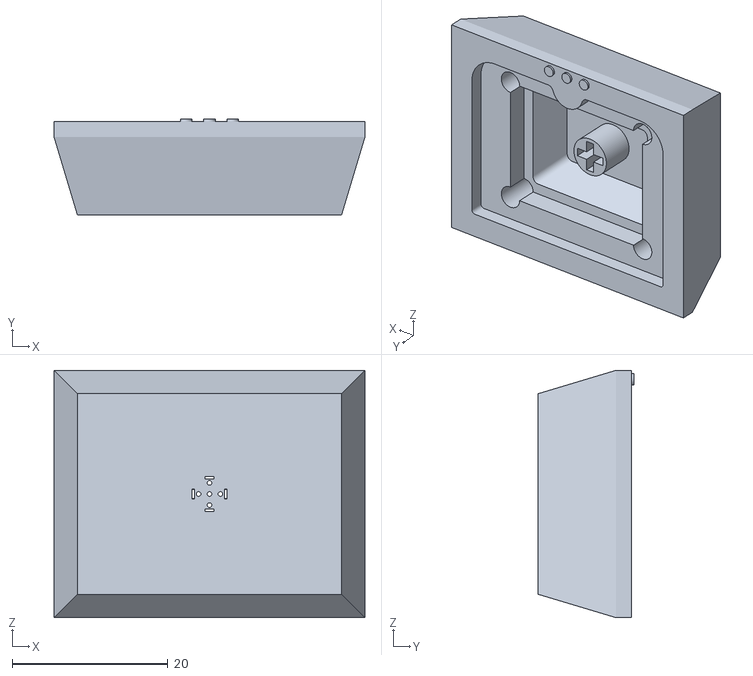
[picture p90: CAD file, 2023-01-14]
MX/1-25u/V2/StemCavity.stl
40.0 x 12.3 x 31.8
