imyownyear/Z-Butt/MX/2-00u/V2/StemCavity-Recessed.stl

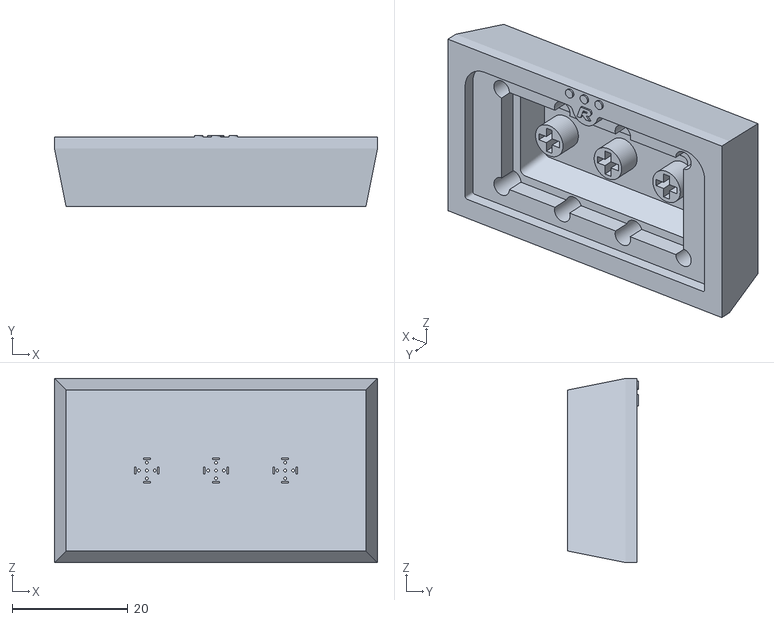
[picture p92: CAD file, 2023-01-14]
MX/2-00u/V2/StemCavity-Recessed.stl
55.8 x 12.3 x 31.8
