imyownyear/Z-Butt/MX/2-75u/V2/SculptingBase.stl

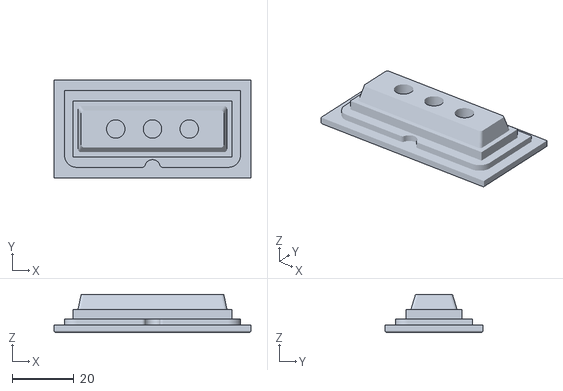
[picture p93: CAD file, 2023-01-14]
MX/2-75u/V2/SculptingBase.stl
64.0 x 31.8 x 12.5
