imyownyear/Z-Butt/MX/6-25u/V2/Reservoir.stl

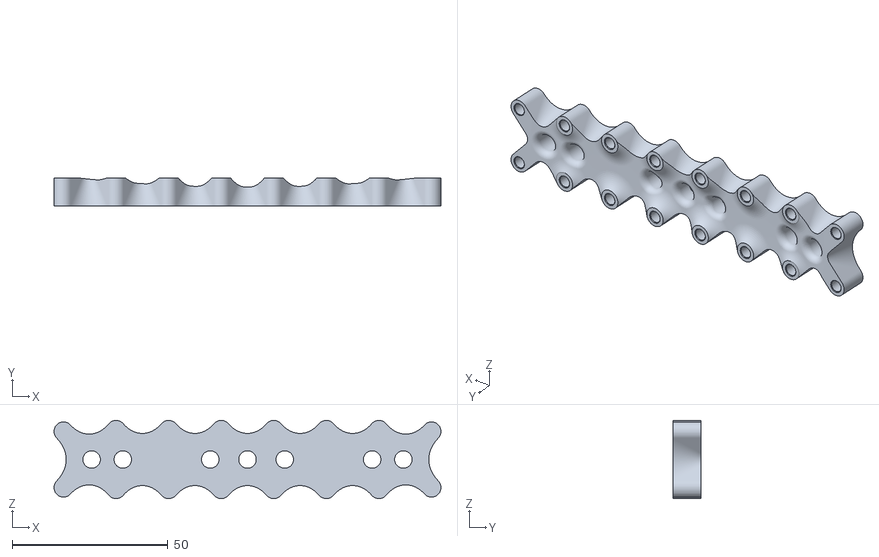
[picture p94: CAD file, 2023-01-14]
MX/6-25u/V2/Reservoir.stl
124.2 x 9.00 x 25.1
