imyownyear/Z-Butt/MX/6-50u/Zbutt-SculptingBase-6.5u.stl

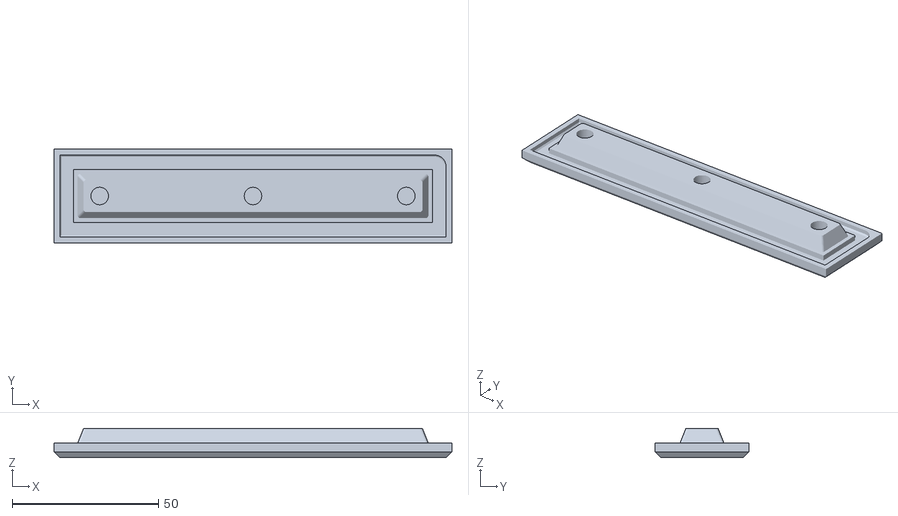
[picture p95: CAD file, 2021-09-03]
MX/6-50u/Zbutt-SculptingBase-6.5u.stl
136.0 x 32.0 x 10.0
