imyownyear/Z-Butt/NoHassleContainer/1.75U-2.00U-No-Hassle.STL

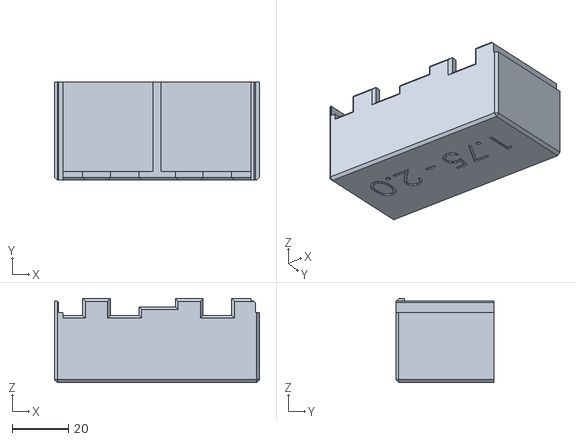
[picture p96: CAD file, 2020-07-30]
NoHassleContainer/1.75U-2.00U-No-Hassle.STL
73.0 x 35.0 x 30.0
