imyownyear/Z-Butt/CloneRiser/1U/ZButt_1U_CloneRiser_Cavity.stl

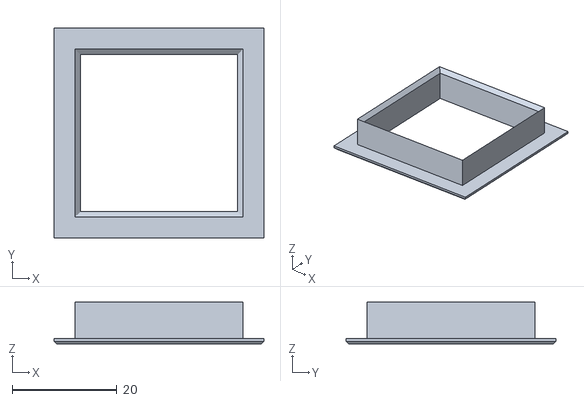
[picture p97: CAD file, 2019-08-20]
CloneRiser/1U/ZButt_1U_CloneRiser_Cavity.stl
40.0 x 40.0 x 8.00
