imyownyear/Z-Butt/MX/1-00u/1u - Production/ZButt-StemCavity-2x2-Recessed.stl

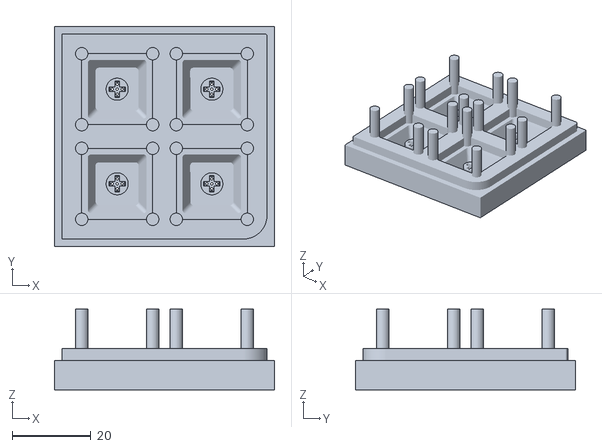
[picture p98: CAD file, 2021-06-11]
MX/1-00u/1u - Production/ZButt-StemCavity-2x2-Recessed.stl
55.8 x 55.8 x 20.5
