imyownyear/Z-Butt/MX/1-00u/1u-V2/Sculpting-Helper-Plus-p1.stl

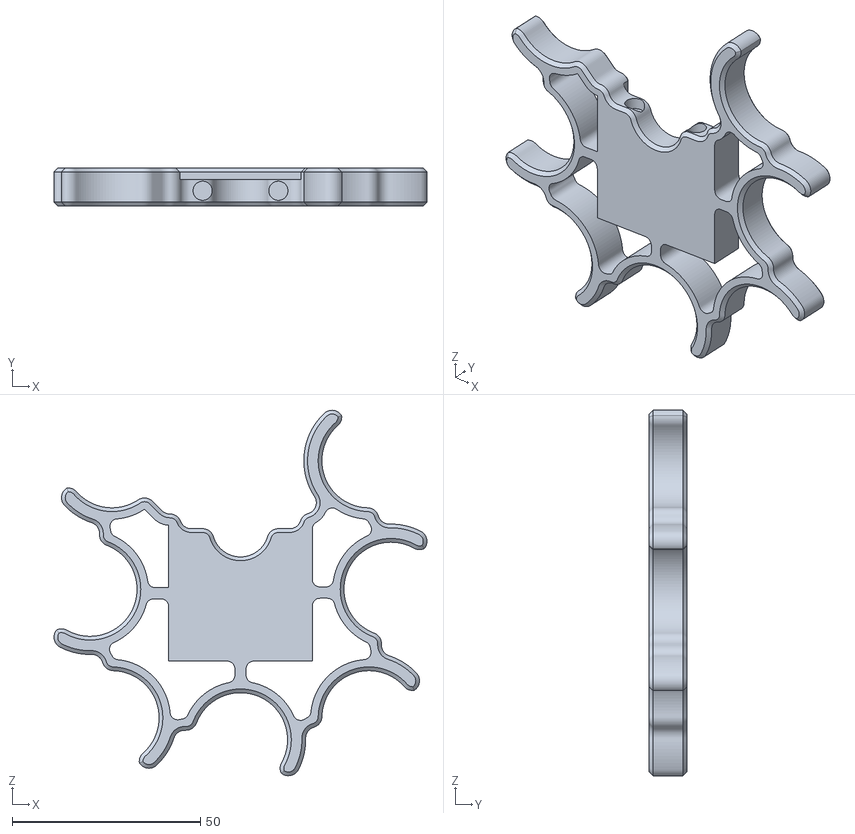
[picture p99: CAD file, 2021-03-12]
MX/1-00u/1u-V2/Sculpting-Helper-Plus-p1.stl
99.1 x 10.0 x 97.1
