imyownyear/Z-Butt/MX/1-50u/V2/SculptingBase.stl

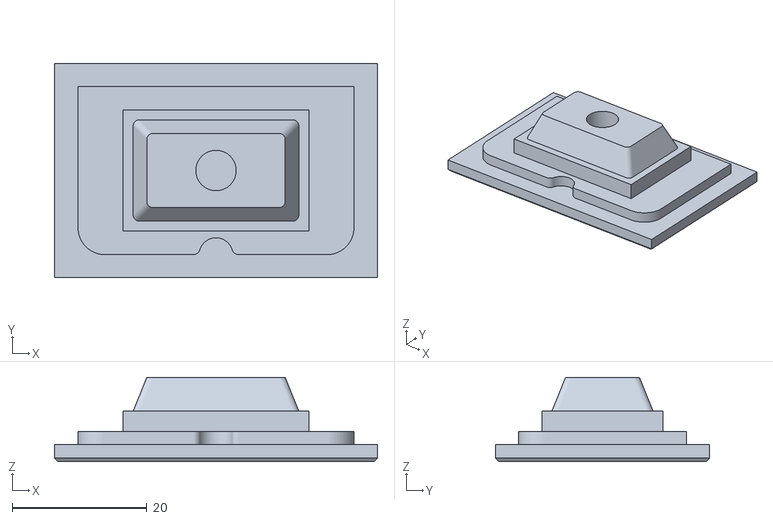
[picture p100: CAD file, 2023-01-14]
MX/1-50u/V2/SculptingBase.stl
48.0 x 31.8 x 12.5
