imyownyear/Z-Butt/MX/2-25u/V2/SculptingBase.stl

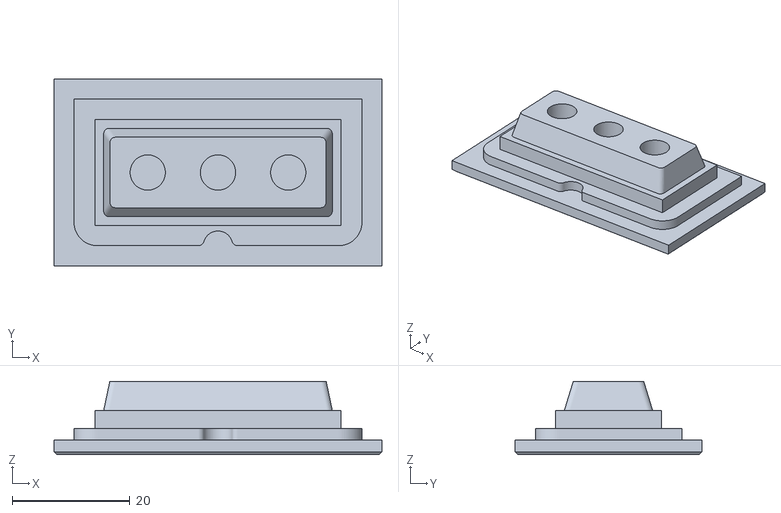
[picture p101: CAD file, 2023-01-14]
MX/2-25u/V2/SculptingBase.stl
55.8 x 31.8 x 12.5
