imyownyear/Z-Butt/NoHassleContainer/2.25U-No-Hassle.STL

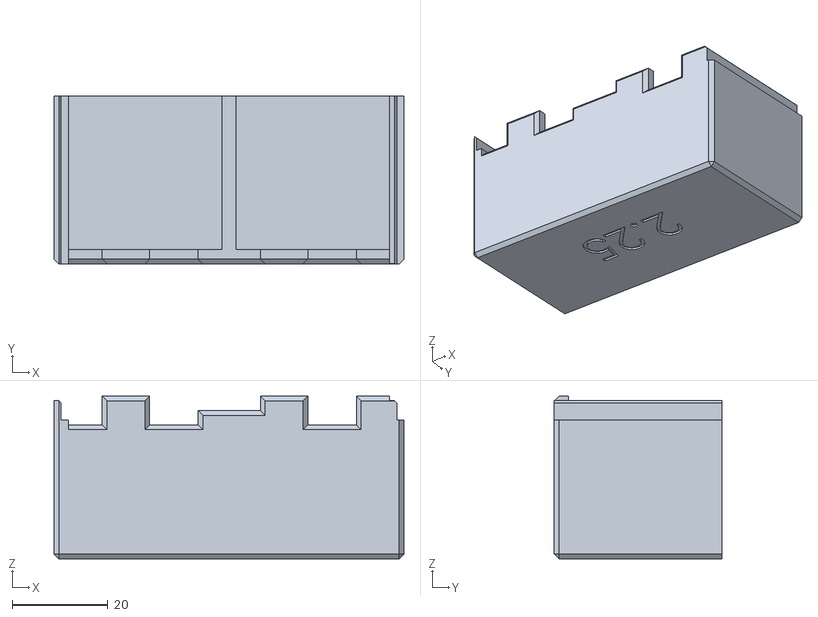
[picture p103: CAD file, 2020-07-30]
NoHassleContainer/2.25U-No-Hassle.STL
73.0 x 35.0 x 34.0
