imyownyear/Z-Butt/MX/1-00u/1u - Production/ZButt-MasterBase-2x5.stl

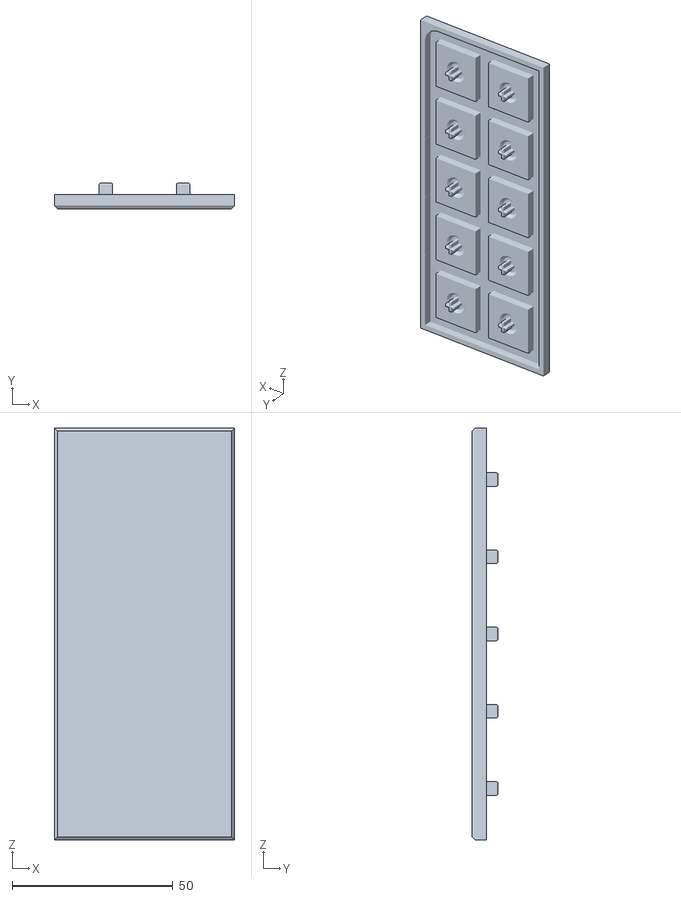
[picture p104: CAD file, 2021-06-11]
MX/1-00u/1u - Production/ZButt-MasterBase-2x5.stl
56.0 x 8.00 x 128.0
