imyownyear/Z-Butt/MX/1-00u/1u-V2/SculptingBase.stl

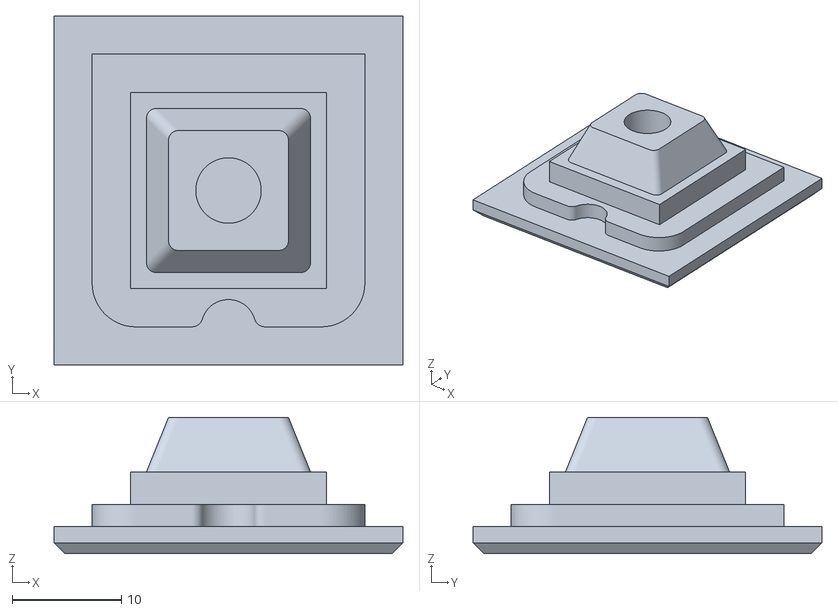
[picture p105: CAD file, 2021-03-12]
MX/1-00u/1u-V2/SculptingBase.stl
32.0 x 32.0 x 12.5
