imyownyear/Z-Butt/NoHassleContainer/noHassle-SpacebarExtend.stl

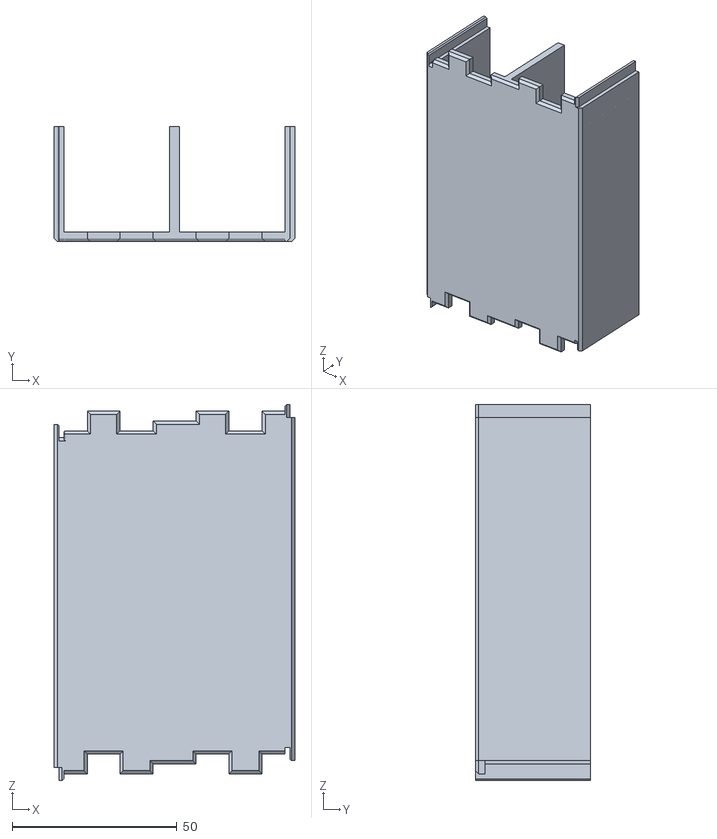
[picture p106: CAD file, 2020-04-01]
NoHassleContainer/noHassle-SpacebarExtend.stl
73.0 x 35.0 x 114.0
