imyownyear/Z-Butt/MX/1-00u/1u-V2/Sculpting-Helper-Plus-p2.stl

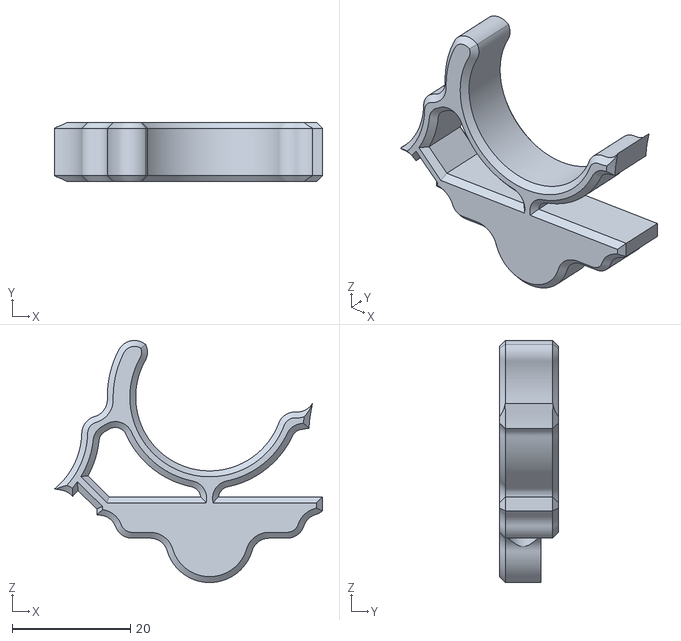
[picture p107: CAD file, 2021-03-12]
MX/1-00u/1u-V2/Sculpting-Helper-Plus-p2.stl
45.4 x 10.0 x 41.0
