imyownyear/Z-Butt/NoHassleContainer/NoHassle-Extender#1.stl

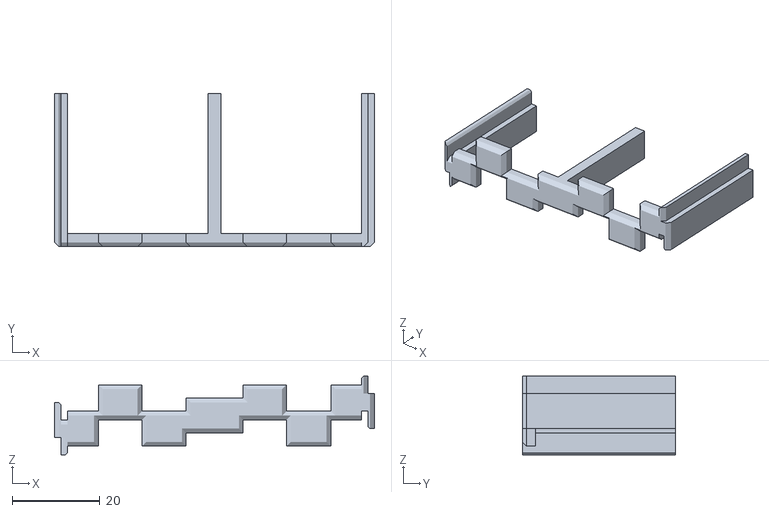
[picture p108: CAD file, 2020-04-01]
NoHassleContainer/NoHassle-Extender#1.stl
73.0 x 35.0 x 18.0
