imyownyear/Z-Butt/MX/1-00u/1u - Production/ZButt-StemCavity-2x5.stl

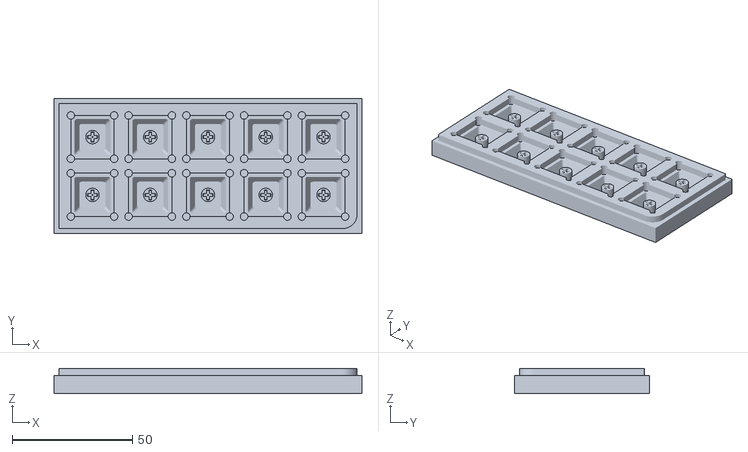
[picture p109: CAD file, 2020-11-21]
MX/1-00u/1u - Production/ZButt-StemCavity-2x5.stl
128.0 x 56.0 x 10.5
