imyownyear/Z-Butt/NoHassleContainer/NoHassle-Extender#2.stl

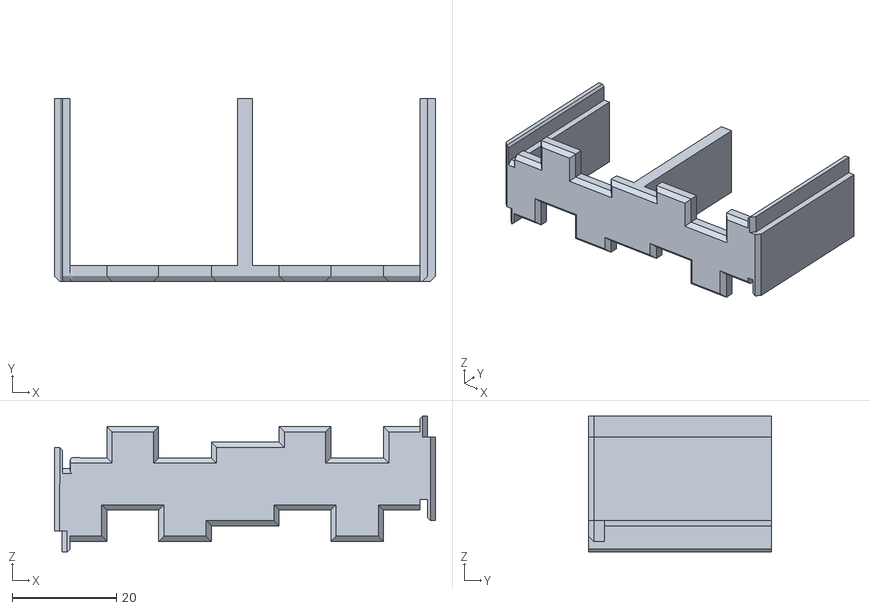
[picture p110: CAD file, 2020-04-01]
NoHassleContainer/NoHassle-Extender#2.stl
73.0 x 35.0 x 26.0
