imyownyear/Z-Butt/MX/1-00u/1u - Production/ZButt-NoHassle-2x2.stl

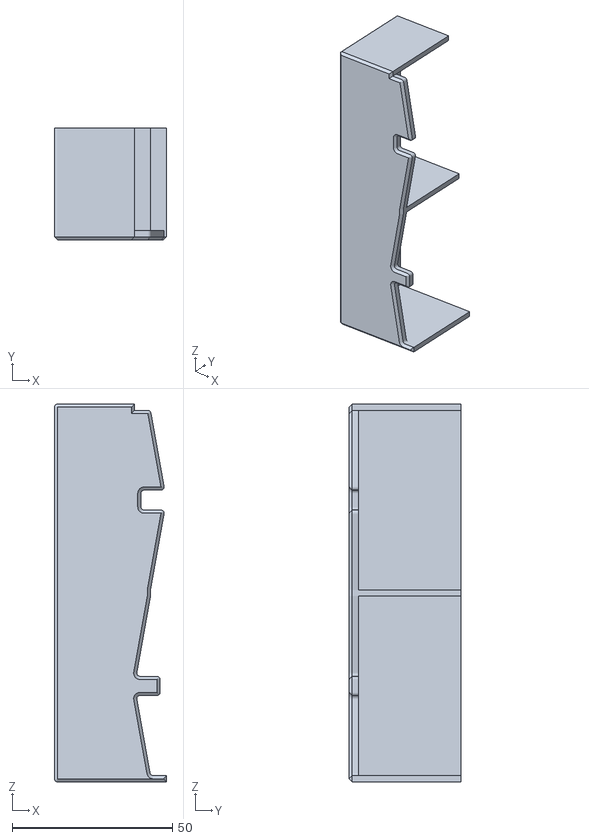
[picture p111: CAD file, 2020-11-21]
MX/1-00u/1u - Production/ZButt-NoHassle-2x2.stl
35.0 x 35.0 x 118.0
