imyownyear/Z-Butt/NoHassleContainer/NoHassle-Extender#3.stl

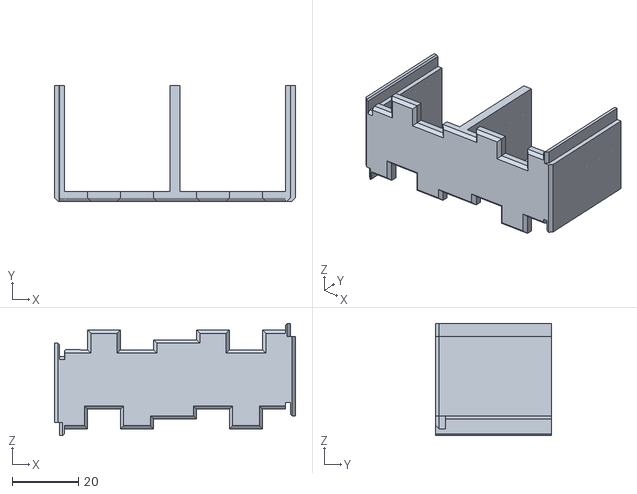
[picture p112: CAD file, 2020-04-01]
NoHassleContainer/NoHassle-Extender#3.stl
73.0 x 35.0 x 34.0
