imyownyear/Z-Butt/MX/1-00u/1u - Production/ZButt-MasterBase-2x2.stl

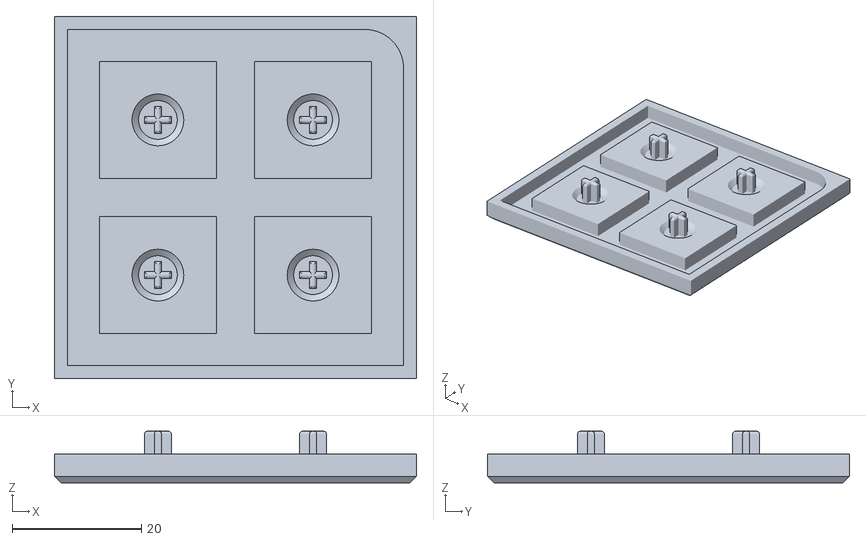
[picture p113: CAD file, 2020-11-21]
MX/1-00u/1u - Production/ZButt-MasterBase-2x2.stl
56.0 x 56.0 x 8.00
