imyownyear/Z-Butt/NoHassleContainer/NoHassle-Joiner.stl

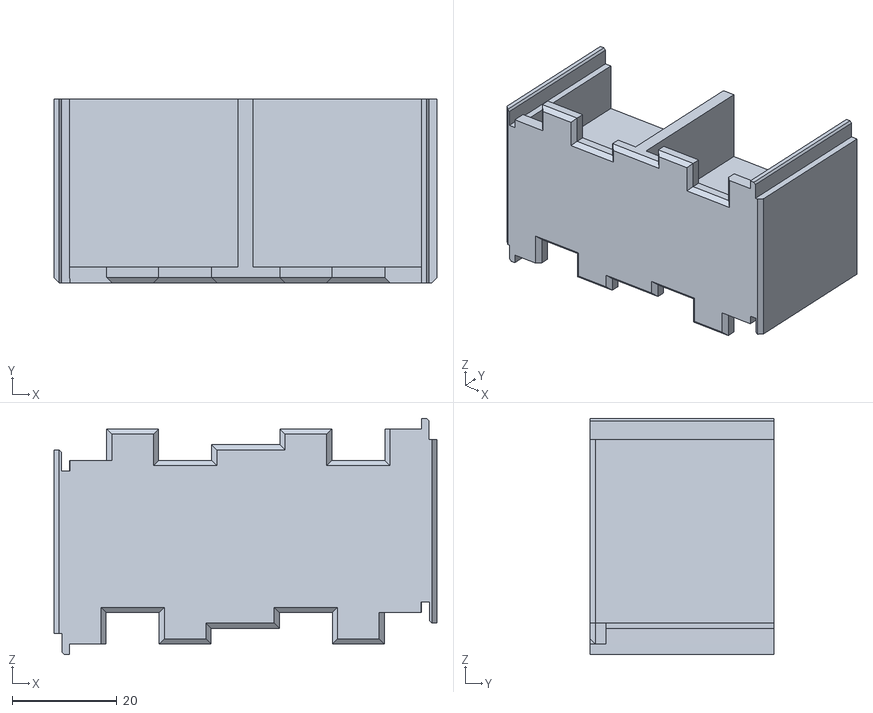
[picture p114: CAD file, 2020-04-01]
NoHassleContainer/NoHassle-Joiner.stl
73.0 x 35.0 x 45.0
