imyownyear/Z-Butt/MX/1-00u/1u - Production/NoHassle2x5Extend.stl

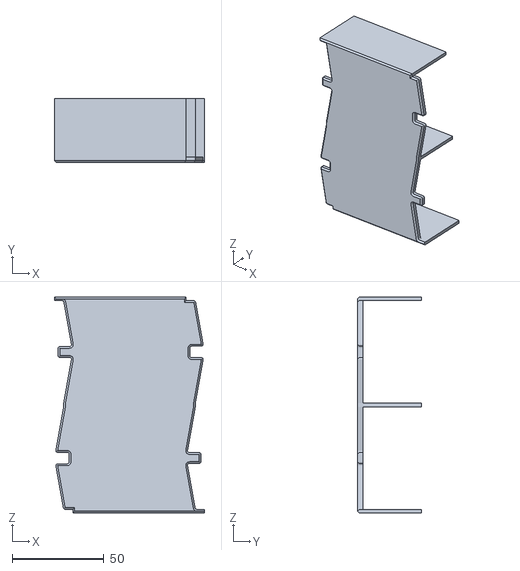
[picture p115: CAD file, 2020-11-21]
MX/1-00u/1u - Production/NoHassle2x5Extend.stl
82.0 x 35.0 x 118.0
