imyownyear/Z-Butt/NoHassleContainer/1U-No-Hassle.stl

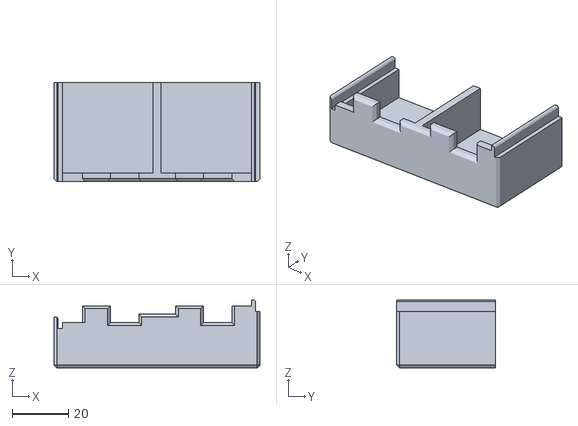
[picture p116: CAD file, 2019-06-23]
NoHassleContainer/1U-No-Hassle.stl
73.0 x 35.0 x 24.0
